tsedlmeier/Synthesizer/Ausarbeitung/src/content/5_VCO.tex

\chapter{VCO}
\label{ch:VCO}
\section{Allgemeines}

Der VCO stellt die Basis aller analogen Synthesizers da. 
Mit einem spannungsgesteuerten Oszillator lassen sich verschiedene Signale generieren, deren Frequenz sich mit der angelegten Steuerspannung verändert.
Analoge Synthesizer orientieren sich oft am 1V/Oktave-Standard.
Dieser besagt, dass sich die Frequenz des Signals mit jedem Volt verdoppelt.
Dies ist von Vorteil, da das Verhältnis zwischen Musiknoten und deren zugeordneten Frequenzen ebenfalls exponentiell ist.
Die tiefste C-Note entspricht beispielsweise einer Frequenz von 16,35 Hz.
Wenn man eine Oktave nach oben geht, verdoppelt sich die Frequenz beim nächsten C auf etwa 32 Hz. Typische Signale bei analogen Synthesizern können der Abbildung \ref{fig:Waveforms} entnommen werden. \cite{MakeSynth}

\begin{figure}[h]
	\centering
	\setlength{\fboxsep}{1pt} %Abstand der Linien zur Abbildung
	\setlength{\fboxrule}{1pt} %Dicke der Linie
	\fbox{}
	\caption{Typische Signale bei analogen Synthesizern \cite{MakeSynth}}
	\label{fig:Waveforms}
\end{figure}

Bei dieser Umsetzung des VCOs wurde sich auf die Realisierung eines Sägezahn- und eines Rechtecksignals konzentriert, da diese aufgrund ihrem hohen Oberwellenanteil markant-hörbare Geräusche erzeugen.
Ein Sinussignal hingegen stellt einen harmonischen Verlauf dar, der sich ebenfalls im Klang äußert.
Hörbare Schwingungen werden mithilfe einer Oszillatorschaltung realisiert, auf die im Folgenden näher eingegangen wird.

\begin{figure}[h]
	\centering
	\setlength{\fboxsep}{1pt} %Abstand der Linien zur Abbildung
	\setlength{\fboxrule}{1pt} %Dicke der Linie
	\fbox{}
	\caption{Oszillatorschaltung}
	\label{fig:Oszillatorschaltung}
\end{figure}

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

\begin{figure}[h]
	\centering
	\setlength{\fboxsep}{1pt} %Abstand der Linien zur Abbildung
	\setlength{\fboxrule}{1pt} %Dicke der Linie
	\fbox{}
	\caption{Oszillator Signalverlauf}
	\label{fig:Oszillator_Signalverlauf}
\end{figure}

\newpage

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

Die verwendete Schaltung in Abbildung \ref{fig:VCO_Stromlaufplan} ist zu großen Teilen an ein \textit{DIY VCO Kit} von Moritz Klein und Erica Synths angelehnt und wird im Folgenden näher erklärt. \cite{vco_manual}

\section{Schaltplan}
Wie im vorherigen Kapitel erläutert, erfolgt die Veränderung der Frequenz der Sägezahnschwingung (vgl. Abbildung  \ref{fig:Oszillator_Signalverlauf}) mithilfe eines NPN-Transistors, welcher im ersten Bereich des Schaltplans zu sehen ist. 
Der davor geschaltene PNP-Transistor dient zur Temperaturkompensation und fungiert als Emitterfolger, indem die an seiner Basis anliegende Spannung an den Emitter kopiert wird.
Allerdings ist die am Emitter des PNP-Transistors anliegende Spannung um der Schwellspannung des Transistors höher.
Bei Versuchen an der realen Schaltung betrug diese etwa 500 mV.
Um den gewünschten Spannungsbereich an der Basis des NPN-Transistors von etwa 350 -- 550 mV zu erreichen, muss das Potentiometer für die Einstellung der Basisspannung der Transistoren auch negative Spannungswerte liefern.

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

Um die resultierende Sägezahnschwingung nach außen führen zu können, wird ein entsprechender Buffer benötigt, der durch einen Operationsverstärker realisiert wird.
Dies ist zwingend notwendig, da ansonsten in die Funktionsweise der Oszillatorschaltung eingegriffen wird. 
Dieser Buffer befindet sich im dritten Bereich des Schaltplans.
Weiterhin wird eine AC-Kopplung mithilfe des Kondensators C2 und dem Widerstand R10 realisiert. 
Diese wird benötigt um eine eventuelle Offset-Spannung der Sägezahnspannung zu entfernen, damit das Signal um den definierten Pegel von 0 V schwingt.

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

Im fünften Bereich des Schaltplans erfolgt die Anpassung auf einen definierten Pegel von 10 V peak-to-peak. 
Da die Sägezahnschwingung eine geringe Spannung aufweist, wird diese mithilfe einer nicht invertierenden Verstärkerschaltung vergrößert und an den Klinkenbuchsenausgang \textit{SAW\_OUT} geführt. 
Da der Spannungspegel des Rechtecksignals durch die Komperatorschaltung verstärkt wurde, muss dieser mithilfe eines Spannungsteilers (R15, R18) entsprechend reduziert werden. 
Schließlich wird das Ausgangssignal durch einen Buffer an den Ausgang \textit{PULSE\_OUT} geführt.

Der nicht eingerahmte Bereich im Schaltplan umfasst die Spannungsversorgung. 
Mihilfe von Schottky-Dioden (D2, D3) wird der Verpolungsschutz der Eingangsspannung von $\pm$12 V gewährleistet. 
Durch die Stützkondensatoren (C3 -- C7) wird die Versorgungsspannung sowohl am Eingang der Spannungsversorgung am Wannenstecker als auch an den IC-Pins stabilisiert.
Weiterhin werden nicht verwendete Eingänge des Schmitt-Triggers mit Masse verbunden.

In der folgenden Tabelle werden die Ein- und Ausgabeelemente des VCOs zusammengefasst:

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

Nachdem die Funktionsweise der Schaltung auf einem Breadboard verifiziert wurde, wird ein Platinenlayout erstellt.
Auf die Vorgehensweise bei der Layouterstellung wird im folgenden Kapitel näher eingegangen.

\newpage
\begin{figure}[h]
\centering
\includepdf[angle=270, clip, trim=1cm 0.8cm 0.8cm 0.8cm, scale=0.8] {figures/VCO_Stromlaufplan_v2_unterteilt.pdf}
%\caption{In Bereiche unterteilter Schaltplan des Sequenzers}
\caption{Schaltplan VCO}
\label{fig:VCO_Stromlaufplan}
\end{figure}

\newpage

\section{Platine}
Nachdem der Schaltplan in Fusion 360 erstellt wurde und mit dem ERC (Electrical Rule Check)-Tool validiert wurde, erfolgt die Erstellung des Platinenlayouts (siehe Abbildung \ref{fig:VCO Layout}).
Die äußeren Abmaße der Platine sind in Bezug auf die Höhe eines \textit{Euro Racks} von 128,5 mm beschränkt. 
Gewählt wurde eine Platinenhöhe von 100 mm, damit ausreichend Platz zur Befestigung der Leiterplatte gewährleistet ist.

%\begin{figure}[h]
%	\centering
%	\setlength{\fboxsep}{1pt} %Abstand der Linien zur Abbildung
%	\setlength{\fboxrule}{1pt} %Dicke der Linie
%	\fbox{\includegraphics[width=0.5\textwidth]{figures/VCO_Layout}}
%	\caption{VCO Layout in Fusion 360}
%	\label{fig:VCO Layout}
%\end{figure}

\begin{figure}[h]
	\centering
	\begin{subfigure}{.5\textwidth}
		\centering
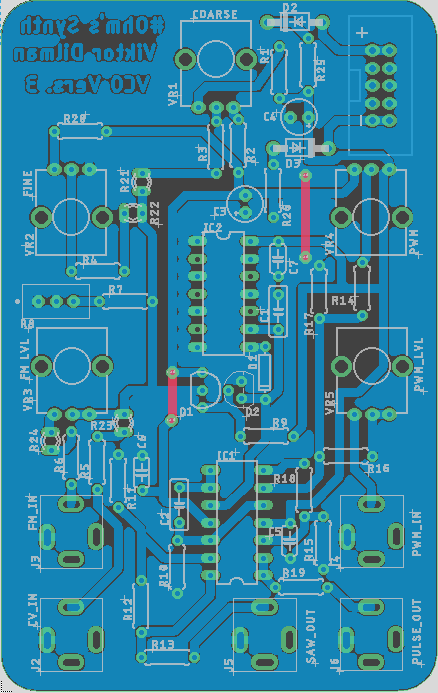
[picture p15: Ausarbeitung/src/figures/VCO_Layout_Front.png]
		
		\caption{Vorderseite}
		\label{fig:VCO_Leiterplatte_vorne}
	\end{subfigure}%
	\begin{subfigure}{.5\textwidth}
		\centering
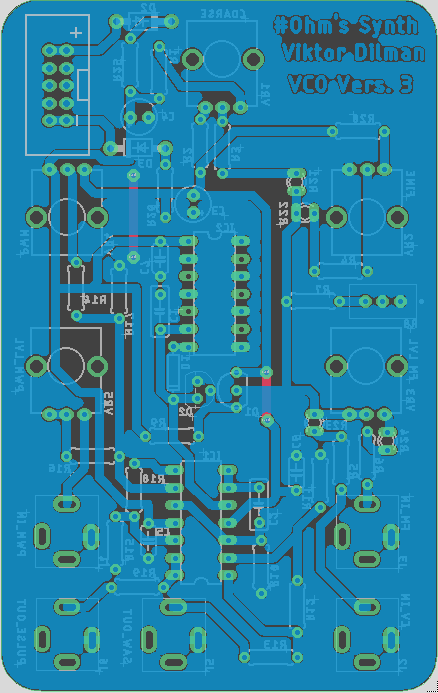
[picture p16: Ausarbeitung/src/figures/VCO_Layout_Back.png]
		
		\caption{Rückseite}
		\label{fig:VCO_Leiterplatte_hinten}
	\end{subfigure}
	\caption{VCO Layout in Fusion 360}
	\label{fig:VCO Layout}
\end{figure}

Die Bauteile wurden einerseits so positioniert, dass die Leiterbahnen möglichst kurz und überschneidungsfrei verlegt werden können.
Andererseits wurden die Potentiometer und Klinkenbuchsen logisch so angeordnet dass die zu einer Einbauklinkenbuchse gehörenden Potentiometer übereinander liegen.
Weiterhin wurde darauf geachtet, dass die Transistoren für die Temperaturkompensation möglichst nah aneinander positioniert werden.
Zudem sind die Stützkondensatoren der ICs möglichst nah an den Versorgungspins der Bauteile zu positionieren.

Bei der Erstellung der Platine wurde darauf geachtet möglichst eine Layer zu verwenden, um die Platine mit einer Platinenfräse herstellen zu können.
Dies ist von Vorteil, da bei der professionellen Anfertigung von Platinen von der Bestellung bis zur Lieferung einige Wochen vergehen können.
Ist der Zugang zu einer Fräse gegeben, kann die erstellte Platine sofort getestet und eventuelle Fehler ausgebessert werden.

Damit die Leiterplatte mit einer Platinenfräse angefertigt werden kann, ist eine relativ dicke Leiterbahnbreite erforderlich. 
Gewählt wurde deshalb eine Leiterbrahnbreite von 50 mil.
An den Stellen, an denen die Leiterbahnen nicht überschneidungsfrei verlegt werden konnten, wurden \textit{Vias} hinzugefügt und die Leiterbahn auf der anderen Seite fortgeführt.
Auf der gefrästen Platinen (siehe Abbildung \ref{fig:VCO Leiterplatte gefraest}) können diese \textit{Vias} mit Brücken verbunden werden.

\begin{figure}[h]
	\centering
	\setlength{\fboxsep}{1pt} %Abstand der Linien zur Abbildung
	\setlength{\fboxrule}{1pt} %Dicke der Linie
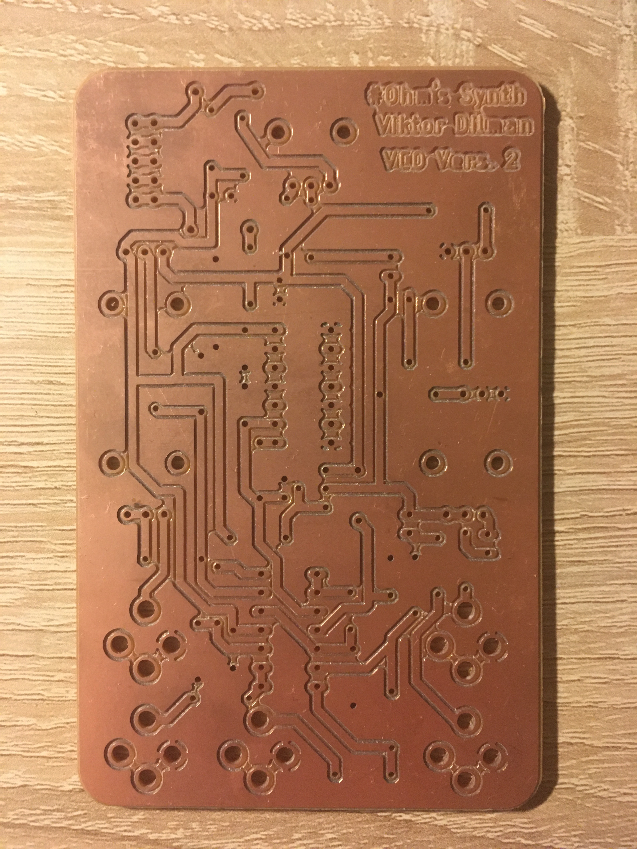
[picture p17: Ausarbeitung/src/figures/VCO_Leiterplatte_gefraest.JPG]
	\fbox{}
	\caption{Gefräste VCO Leiterplatte}
	\label{fig:VCO Leiterplatte gefraest}
\end{figure}

Da für die verwendeten Einbauklinkenbuchsen keine passende Bibliothek existiert, musste diese manuell angelegt werden.
Dafür wurde ein Symbol einer ähnlichen Klinkenbuchse verwendet und das Footprint nach dem Datenblatt des Herstellers erstellt wie in Abbildung \ref{fig:Einbauklinkenbuchse in Fusion 360} zu sehen. \cite{cliff}

\begin{figure}[h]

\end{figure}

\begin{figure}[h]
	\centering
	\begin{subfigure}{.5\textwidth}
	\centering
	\setlength{\fboxsep}{1pt} %Abstand der Linien zur Abbildung
	\setlength{\fboxrule}{1pt} %Dicke der Linie
	\fbox{}
	\caption{Verwendetes Symbol}
	\label{fig:Klinkenbuchse Symbol}
	\end{subfigure}%
	\begin{subfigure}{.5\textwidth}
	\centering
	\setlength{\fboxsep}{1pt} %Abstand der Linien zur Abbildung
	\setlength{\fboxrule}{1pt} %Dicke der Linie
	\fbox{}
	\caption{Erstelltes Footprint}
	\label{fig:Klinkenbuchse Footprint}
	\end{subfigure}
	\caption{Erstellung der Einbauklinkenbuchse in Fusion 360}
	\label{fig:Einbauklinkenbuchse in Fusion 360}
\end{figure}

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

\begin{figure}[h]
	\centering
	\begin{subfigure}{.5\textwidth}
		\centering
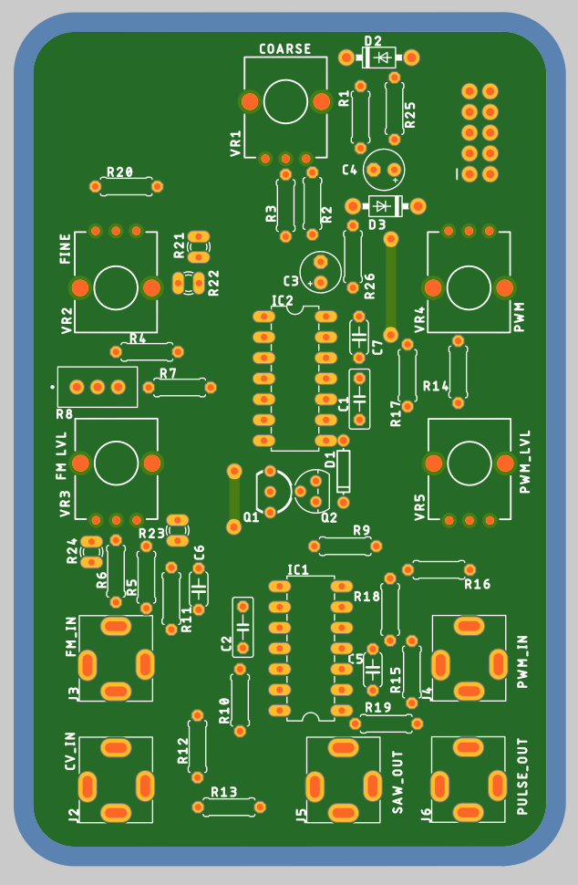
[picture p18: Ausarbeitung/src/figures/VCO_Rendering_Front.png]
		
		\caption{Vorderseite}
		\label{fig:VCO_Front}
	\end{subfigure}%
	\begin{subfigure}{.5\textwidth}
		\centering
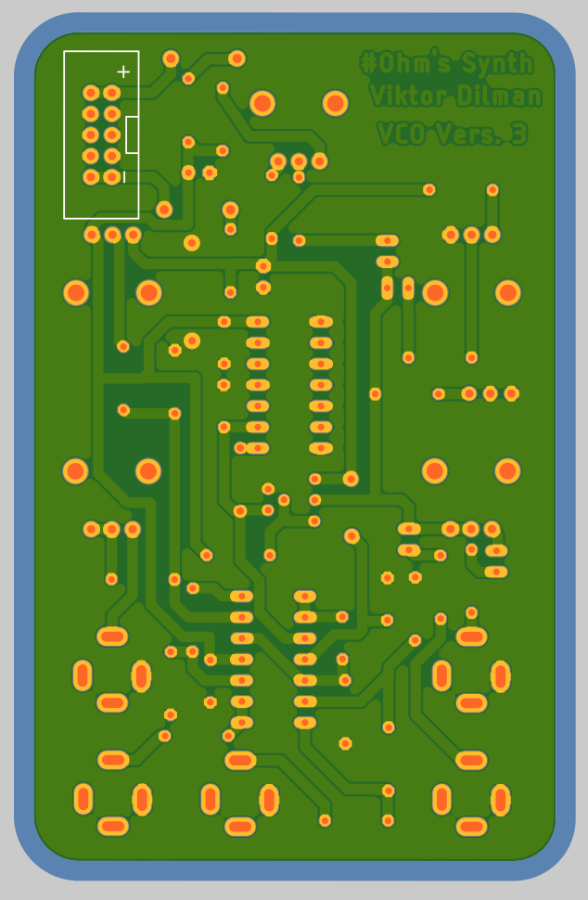
[picture p19: Ausarbeitung/src/figures/VCO_Rendering_Back.png]
		
		\caption{Rückseite}
		\label{fig:VCO_Back}
	\end{subfigure}
	\caption{VCO Leiterplatte}
	\label{fig:VCO Leiterplatte}
\end{figure}

\newpage
\section{Mechanischer Aufbau}
Mithilfe der \textit{Fusion 360}-Funktionalität der Übertragung einer 2D- auf eine 3D-Leiterplatte wurde eine Abdeckung konstruiert (siehe Abbildung \ref{fig:VCO Frontplattemit 3D-Leiterplatte}).
Dies hat den Vorteil, dass für die Potentiometer und Klinkenbuchsen die Aussparungen an der Frontplatte exakt positioniert werden können.
Die Abdeckplatte wird mithilfe von Gewindeschrauben der Einbauklinkenbuchsen an die Platine befestigt.
Weiterhin werden auf die Potentiometer Abdeckkappen angebracht, die zusätzlichen Halt bieten.
An den Ecken der Frontplatte werden Aussparungen vorhergesehen, um das Modul in einem Eurorack-Gehäuse befestigen zu können.
Schließlich wird die Frontplatte aus Plexiglas mit einem \textit{Laser-Cutter} gefertigt.

\begin{figure}[h]
	\centering
	\setlength{\fboxsep}{1pt} %Abstand der Linien zur Abbildung
	\setlength{\fboxrule}{1pt} %Dicke der Linie
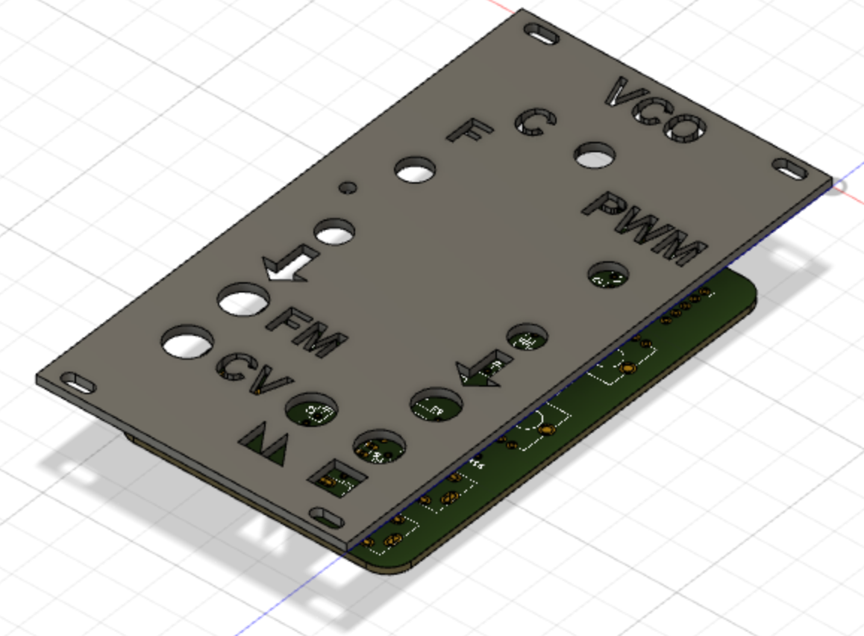
[picture p20: Ausarbeitung/src/figures/VCO_Frontplatte_schraeg.png]
	\fbox{}
	\caption{VCO Frontplatte schräg mit Leiterplatte}
	\label{fig:VCO Frontplattemit 3D-Leiterplatte}
\end{figure}

%\begin{figure}[h]
%	\centering
%	\setlength{\fboxsep}{1pt} %Abstand der Linien zur Abbildung
%	\setlength{\fboxrule}{1pt} %Dicke der Linie
%	\fbox{\includegraphics[width=0.35\textwidth]{figures/VCO_Frontplatte_oben}}
%	\caption{VCO Frontplatte, Vorderansicht}
%	\label{fig:VCO Frontplatte}
%\end{figure}
