tsedlmeier/Synthesizer/Sonstiges/LPDES/VCO_Studienarbeit_Latex/Änderung in thesis.tex und cover.txt

Die Welt der Technik befindet sich seit Beginn in einem ständigen Wandel. Neben immer komplexer und kleinerer werdender Hardware steigen auch stetig die Anforderung bezüglich leistungsfähiger und flexibler Software. Besonders die Verarbeitungsgeschwindigkeit und Reaktionsfähigkeit von Software-Systemen rückt dabei zunehmend in den Fokus. So haben in den Anfangszeiten der Informatik gerade sequentiel oder seriel abarbeitende Programme Anwendung gefunden. Dies bedeutet, dass jeder Befehl Zeile für Zeile abgearbeitet wurde. Die Abarbeitung entspricht einem linearen Vorgehen. Für viele Anwendungen ist dieses Verhalten jedoch gänzlich ungeeignet. Somit etablierte sich neben der sequentiellen Abarbeitung zunehmend die parallele oder quasiparallele Abarbeitung. Gerade bei den heutigen Mikrocontroller- oder Prozessor-Familien werden mit geschickten Scheduling-Mechanismen die vielfälltig einsetzbaren eingebetten Systeme, die beinahe in jeden Bereich des Altags vorgedrungen sind, erst möglich. In Python sind diese Werkzeuge in Form von Koroutinen, Threads oder Asnychio auf Programmierebene gegeben. Sinnvoll und bedacht eingesetzt können sie merkliche Geschwindigkeits- und Flexibilitätsvorteile für den Anwender erbringen.\\
Neben der grundlegenden theoretischen Erläuterung der verscheidenen Konzepte sollen durch die nähere Betrachtung eines exemplarischen Anwendungsfalls die Zusammenhänge besser verdeutlicht werden.
