tsedlmeier/Synthesizer/Sonstiges/LPDES/VCO_Studienarbeit_Latex/thesis-template-master/thesis.tex

\documentclass[
    11pt,
    a4paper,
    egregdoesnotlikesansseriftitles,
    toc=chapterentrywithdots,
    openany,
    oneside,
    titlepage,
    parskip=half,
    headings=normal,  % reduces heading size
    listof=totoc,
    bibliography=totoc,
    index=totoc,
    captions=tableheading,  % caption below table
    chapterprefix,
    listof=flat,
    final
]{scrbook}

% details about your thesis
\newcommand{\titel}{
	Entwicklung eines modularen Synthesizers: Voltage Controlled Oscillator}
\newcommand{\artderarbeit}{Studienarbeit}  % {Projektarbeit, Bachelorarbeit,Masterarbeit}
\newcommand{\autor}{
	%Altaher Ahmad, Balbach Thomas, 
	Dilman Viktor
	%, Kirschner Christoph, Sedlmeier Toni 
}
\newcommand{\studiengang}{Fach Leiterplattendesign}  % {Informatik,Wirtschaftsinformatik,Medieninformatik}
%\newcommand{\ausgabe}{22.12.2022}
\newcommand{\abgabe}{ 22.12.2022}
\newcommand{\erstgutachter}{
	%Prof. Dr.Alexander von Hoffmann 
	M.Eng. Eduard Bluoss
}
\newcommand{\logo}{figures/TH-Nuernberg-RGB.png}
\newcommand{\keywords}{hot, fuzz}

% custom head and foot
\usepackage[automark]{scrlayer-scrpage}
\pagestyle{scrheadings}
\ihead{\headmark}
\chead{}
\ohead{\pagemark}
\renewcommand*\chaptermarkformat{\chapappifchapterprefix{\ }% 
  \thechapter.\enskip}

\usepackage{titlesec}

\RedeclareSectionCommand[tocindent=0pt]{section}
\RedeclareSectionCommand[tocindent=0pt]{subsection}
\RedeclareSectionCommand[tocnumwidth=30pt, beforeskip = -30pt]{chapter}

\usepackage{scrhack}

% other packages
\usepackage[utf8]{inputenc}
\usepackage[T1]{fontenc}
\usepackage{lmodern,relsize,textcomp,csquotes}
\usepackage{amsmath,amsfonts}
\usepackage[ngerman,ngerman]{babel}  % flip for German thesis
\usepackage[final]{graphicx}
\usepackage{setspace,geometry,xcolor}
\usepackage{makeidx}
\usepackage{paralist,ifthen,todonotes}
\usepackage{url}
%\usepackage[toc]{glossaries}
\usepackage{pdfpages}
\usepackage[style = numeric, backend = bibtex]{biblatex}
%Für die Nutzung von Abkürzungen
\usepackage{acronym}
%Für die Nutzung von setlist im Abkürzungsverzeichnis
\usepackage{enumitem}

%\usepackage[demo]{graphicx}
\usepackage{caption}
\usepackage{subcaption}

% table setup
\usepackage{longtable}
\usepackage{array}
\usepackage{ragged2e}
\usepackage{lscape}

% pdf hyperref
\usepackage[
    bookmarks=true,
    bookmarksopen=true,
    bookmarksnumbered=true,
    bookmarksopenlevel=1,
    pdftitle={\titel},
    pdfauthor={\autor},
    pdfcreator={\autor},
    pdfsubject={\titel},
    pdfkeywords={\keywords},
    pdfpagelabels=true,
    colorlinks=true,
    linkcolor=red,
    urlcolor=magenta,
    citecolor=cyan,
    filecolor=magenta,
    menucolor=red,
    plainpages=false,
    hypertexnames=true,
    linktocpage=true,
]{hyperref}

% configure your listings style
\usepackage{listings}
\lstset{
	tabsize=3,
	extendedchars=true,
	frame=single,
	showstringspaces=true,
	numbers=left,
	numberstyle=\small,
	breakautoindent=true,
	basicstyle=\small
}

\renewcommand{\lstlistingname}{Auflistung} % Aendert Listing zu Auflistung
\renewcommand{\lstlistlistingname}{Auflistungsverzeichnis} % Aendert Listing zu Auflistung

% page setup
% \setlength{\topskip}{\ht\strutbox}
\geometry{paper=a4paper,left=3cm,top=2cm,right=2cm,bottom=2cm}
\onehalfspacing
\frenchspacing
\clubpenalty = 10000
\widowpenalty = 10000 
\displaywidowpenalty = 10000

% some commands
\newcommand{\ua}{\mbox{u.\,a.\ }}
\newcommand{\zB}{\mbox{z.\,B.\ }}
\newcommand{\dahe}{\mbox{d.\,h.,\ }}
\newcommand{\bzw}{\mbox{bzw.\ }}
\newcommand{\bzgl}{\mbox{bzgl.\ }}
\newcommand{\eg}{\mbox{e.\,g.\ }}
\newcommand{\ie}{\mbox{i.\,e.\ }}
\newcommand{\wrt}{\mbox{w.\,r.\,t.\ }}
\newcommand{\etal}{\mbox{\emph{et.\,al.\ }}}

% load glossary entries
%\makenoidxglossaries
%\loadglsentries{glossary}

%\bibliographystyle{ieeetran}
\bibliography{refs.bib}
\nocite{*}

\begin{document}

\setcounter{secnumdepth}{3}  % numerate subsections
\setcounter{tocdepth}{2}  % ...but don't include them in toc

\frontmatter
\include{cover}\cleardoublepage

%\include{content/0_abstract}\cleardoublepage

%\titleformat{\chapter}
%  {\Large\bfseries} % format
%  {}                % label
%  {0pt}             % sep
%  {\huge}           % before-code
%  
%\tableofcontents\cleardoublepage

\tableofcontents

\include{Abkuerzungsverzeichnis/abkuerzungsverzeichnis}

\listoffigures

\listoftables

\mainmatter
\include{content/1_intro}
\include{content/2_concepts}
%\include{content/3_Netzteil}
%\include{content/4_LFO}
\include{content/5_VCO}
%\include{content/6_Sequenzer}
%\include{content/7_Filter}
%\include{content/8_Mischer}
%\include{content/9_Gehauese}
%\include{content/10_summary}

% remove if not needed
%\appendix
%\include{content/a1_supplemental}

%\backmatter

%\lstlistoflistings
%\cleardoublepage

%\printbibliography
\printbibliography[heading=bibintoc, title={Literaturverzeichnis}]
\end{document}
