tsedlmeier/Synthesizer/Ausarbeitung/src/content/8_Mischer.tex

\chapter{Mischer}
\label{ch:concept}
\section{Allgemeines}
Der Audio Mixer verknüpft verschiedene, von den anderen Bauteilen des modularen Synthesizers erzeugte Eingangssignale (Klangquellen) miteinander. Das heißt er mischt, kombiniert und gleicht verschiedene Klänge und Audiosignale aus, wodurch neue Signalformen
und Klänge generiert werden können. Die entstehenden kombinierten Signale werden an den Filter weitergeleitet.

\section{Schaltplan}
Dieser Abschnitt beschreibt den Schaltplan des Mischers in Abbildung \ref{fig:schaltplan_mixer}. 
Dazu werden die einzelnen Teilbereiche des Schaltplans vorgestellt.

IN1-IN3 sind die Audioeingangsbuchsen, INV OUT-CLIP OUT sind die Audio-Ausgangsbuchsen.

Der Teilbereich 1 des Schaltplans ermöglicht die Anpassung der Lautstärke der Signale in jedem Bereich zwischen 0\% und 100\%. 
Ein zentrales Bauteil ist der Vierfach-Operationsverstärker TL074P. Die drei verbauten Potentiometer regeln die Levels der Eingangssignale.

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

\begin{figure}[h]
	\centering
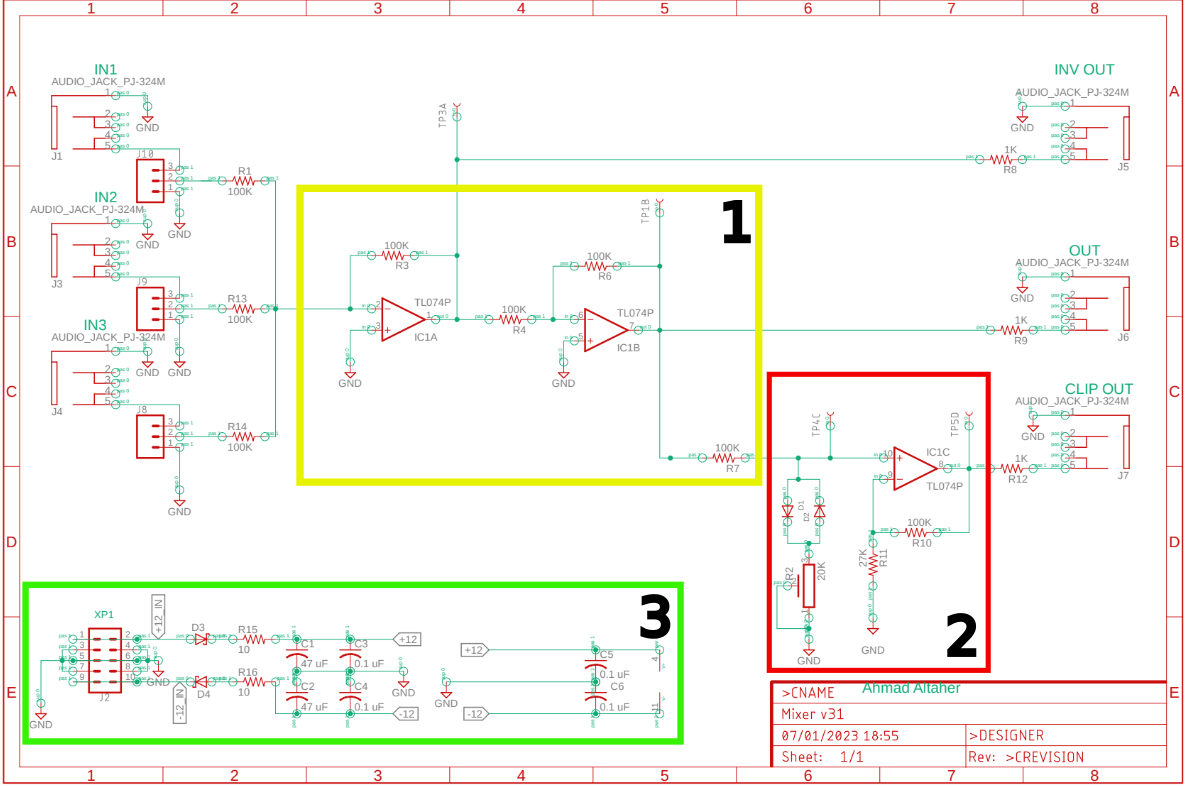
[picture p78: Ausarbeitung/src/figures/SchaltplanMixer_new.png]
	
	\caption{Ausschnitt des Mischer-Schaltplanes aus Fusion360 \cite{mixer_manual}}
	\label{fig:schaltplan_mixer}
\end{figure}
\FloatBarrier

\section{Platine}
\begin{figure}[h]
	\centering
	\setlength{\fboxsep}{1pt} %Abstand der Linien zur Abbildung
	\setlength{\fboxrule}{1pt} %Dicke der Linie
	\fbox{}
	\caption{Ausschnitt des Mischer-Platinen-Layouts aus Fusion360 (Unterseite)}
	\label{fig:platine_mixer}
\end{figure}
\FloatBarrier
