tsedlmeier/Synthesizer/Bauteile/Bauteilliste_Synth_181022.docx

Bauteilliste (zusätzlich zur Moritz-Klein-Bauteilliste), validiert

Bauteil | Stück | | Website | | Artikel-Nr. | Link

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

LFO
Widerstände 220kohm | 20 | | Reichelt | | METALL 220K | https://www.reichelt.de/de/de/widerstand-metallschicht-220-kohm-0207-0-6-w-1--metall-220k-p11628.html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
Widerstände 100kohm | 10 | | Reichelt | | METALL 100K | https://www.reichelt.de/widerstand-metallschicht-100-kohm-0207-0-6-w-1--metall-100k-p11458.html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
Widerstände 51kohm | 20 | | Reichelt | | METALL 51,0K | https://www.reichelt.de/widerstand-metallschicht-51-0-kohm-0207-0-6-w-1--metall-51-0k-p11859.html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
Widerstände 22kohm | 20 | | Reichelt | | METALL 22,0K | https://www.reichelt.de/widerstand-metallschicht-22-0-kohm-0207-0-6-w-1--metall-22-0k-p11622.html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
Widerstände 20kohm | 20 | | Reichelt | | METALL 20,0K | https://www.reichelt.de/widerstand-metallschicht-20-0-kohm-0207-0-6-w-1--metall-20-0k-p11606.html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
Widerstände 10kohm | 20 | | Reichelt | | METALL 10,0K | https://www.reichelt.de/widerstand-metallschicht-10-0-kohm-0207-0-6-w-1--metall-10-0k-p11449.html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
Widerstände 1kohm | 20 | | Reichelt | | METALL 1,00K | https://www.reichelt.de/widerstand-metallschicht-1-00-kohm-0207-0-6-w-1--metall-1-00k-p11403.html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
Widerstände 100Ohm | 20 | | Reichelt | | METALL 100 | https://www.reichelt.de/widerstand-metallschicht-100-ohm-0207-0-6-w-1--metall-100-p11457.html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
Kondensatoren 1uF | 10 | | Reichelt | | Z5U-5 1,0µ | https://www.reichelt.de/vielschicht-keramikkondensator-1-0-20--z5u-5-1-0--p22985.html
Dioden SB140 (Schottky) | 5 | | Reichelt | | SB 140 | https://www.reichelt.de/schottkydiode-40-v-1-a-do-41-sb-140-p16024.html
Transistoren BC548 (NPN) | 5 | | Reichelt | | BC 548C | https://www.reichelt.de/de/de/bipolartransistor-npn-30v-0-1a-0-5w-to-92-bc-548c-p5010.html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
Transistoren BC558 (PNP) | 5 | | Reichelt | | BC 558A | https://www.reichelt.de/de/de/bipolartransistor-pnp-30v-0-1a-0-5w-to-92-bc-558a-p5020.html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
Potentiometer 100k vertikal | 3 | | Reichelt | | RK09K113-LIN100K | https://www.reichelt.de/drehpotentiometer-mono-100-kohm-linear-6-mm-rk09k113-lin100k-p73818.html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
LED GRÜN | 10 | | Reichelt | | LED 5MM ST GN | https://www.reichelt.de/led-5-mm-bedrahtet-gruen-20-mcd-60--led-5mm-st-gn-p6823.html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
LED ROT | 10 | | Reichelt | | LED 5MM ST RT | https://www.reichelt.de/led-5-mm-bedrahtet-rot-5-mcd-60--led-5mm-st-rt-p6821.html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
ICs TL074 | 5 | | Reichelt | | TL 074 DIL | https://www.reichelt.de/operationsverstaerker-4-fach-dip-14-tl-074-dil-p21557.html
EBS 35 Klinkeneinbaubuchse | 5 | | Reichelt | | EBS 35 | https://www.reichelt.de/klinkeneinbaubuchse-3-5-mm-stereo-ebs-35-p7301.html?&trstct=pos_0&nbc=1
Kippschalter, Ein-Ein | 5 | | Reichelt | | GOOBAY 10020 | https://www.reichelt.de/kippschalter-c7584.html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

Sequencer
Widerstände 100kohm | 20 | | Reichelt | | METALL 100K | https://www.reichelt.de/widerstand-metallschicht-100-kohm-0207-0-6-w-1--metall-100k-p11458.html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
Widerstände 68 kohm | 10 | | Reichelt | | YAG 4FTE52-68K | https://www.reichelt.de/widerstand-metallschicht-68-kohm-0204-0-4-w-1--yag-4fte52-68k-p236962.html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
Widerstände 51kohm | 10 | | Reichelt | | METALL 51,0K | https://www.reichelt.de/widerstand-metallschicht-51-0-kohm-0207-0-6-w-1--metall-51-0k-p11859.html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
Widerstände 47 kohm | 10 | | Reichelt | | METALL 47,0K | https://www.reichelt.de/widerstand-metallschicht-47-0-kohm-0207-0-6-w-1--metall-47-0k-p11823.html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
Widerstände 18 kohm | 10 | | Reichelt | | METALL 18,0K | https://www.reichelt.de/widerstand-metallschicht-18-0-kohm-0207-0-6-w-1--metall-18-0k-p11558.html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
Widerstände 6,8 kohm | 10 | | Reichelt | | YAG FTE52-6K80 | https://www.reichelt.de/widerstand-metallschicht-6-8-kohm-0204-0-4-w-1--yag-fte52-6k80-p236939.html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
Widerstände 4,7 kohm | 10 | | Reichelt | | METALL 4,70K | https://www.reichelt.de/widerstand-metallschicht-4-70-kohm-0207-0-6-w-1--metall-4-70k-p11784.html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
Widerstände 1 kohm | 10 | | Reichelt | | METALL 1,00K | https://www.reichelt.de/widerstand-metallschicht-1-00-kohm-0207-0-6-w-1--metall-1-00k-p11403.html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
Widerstände 200 ohm | 10 | | Reichelt | | METALL 200 | https://www.reichelt.de/widerstand-metallschicht-200-ohm-0207-0-6-w-1--metall-200-p11609.html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
Widerstände 10 ohm | 10 | | Reichelt | | METALL 10,0 | https://www.reichelt.de/widerstand-metallschicht-10-0-ohm-0207-0-6-w-1--metall-10-0-p11448.html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
Elektrolytkondensatoren 47uF | 10 | | Reichelt | | RAD LXZ 16/47 | https://www.reichelt.de/elko-radial-47-f-16-v-105-low-esr-5x11-5-mm-rm-2-5-rad-lxz-16-47-p166362.html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
Folienkondensator, 1 µF | 10 | | Reichelt | | ECWFE 1U 450 | https://www.reichelt.de/folienkondensator-1-f-450-v-rm-15-105-c-5--ecwfe-1u-450-p228877.html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
Keramik-Kondensator, 100 nF | 10 | | Reichelt | | KERKO 100N | https://www.reichelt.de/keramik-kondensator-100-nf-20-80-y5v-50-100-v-rm-5-kerko-100n-p9265.html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
Keramik-Kondensator 1,0N | 10 | | Reichelt | | KERKO 1,0N | https://www.reichelt.de/keramik-kondensator-1-0n-kerko-1-0n-p9257.html?&trstct=pol_0&nbc=1
Schottkydiode | 10 | | Reichelt | | SB 140 | https://www.reichelt.de/schottkydiode-40-v-1-a-do-41-sb-140-p16024.html
Dioden 1N4148 | 30 | | Reichelt | | 1N 4148 | https://www.reichelt.de/schalt-diode-100-v-150-ma-do-35-1n-4148-p1730.html?&trstct=pos_0&nbc=1
Bipolartransistor, NPN | 10 | | Reichelt | | 2N 3904 | https://www.reichelt.de/bipolartransistor-npn-40v-0-2a-0-5w-to-92-2n-3904-p2020.html
Bipolartransistor, NPN | 10 | | Reichelt | | BC 547B | https://www.reichelt.de/bipolartransistor-npn-45v-0-1a-0-5w-to-92-bc-547b-p5006.html?&trstct=pos_1&nbc=1
Drehpotentiometer, 250 kOhm, linear, 6 mm | 2 | | Reichelt | | PIH PC16IP06254A | https://www.reichelt.de/drehpotentiometer-250-kohm-linear-6-mm-pih-pc16ip06254a-p232706.html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
Drehpotentiometer, Mono, 100 kOhm, linear, 6 mm | 5 | | Reichelt | | RK09K111-LIN100K | https://www.reichelt.de/drehpotentiometer-mono-100-kohm-linear-6-mm-rk09k111-lin100k-p73810.html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
Kippschalter, Ein-Ein | 10 | | Reichelt | | GOOBAY 10020 | https://www.reichelt.de/kippschalter-c7584.html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
LED 5 mm - Farbe Blau, 100 Stück | 1 | | Reichelt | | QUAD 1802O025 | https://www.reichelt.de/led-5-mm-farbe-blau-100-stueck-quad-1802o025-p280131.html?&trstct=pos_2&nbc=1
ICs TL074 | 5 | | Reichelt | | TL 074 DIL | https://www.reichelt.de/operationsverstaerker-4-fach-dip-14-tl-074-dil-p21557.html
SMD 4017 Counter | 5 | | Reichelt | | 4017BE TEX | https://www.reichelt.de/counter-5-stage-3--18-v-dil-16-cd-4017be-tex-p216643.html?search=cd4017
Potentiometer 5k | 5 | | Reichelt | | 76-10 5,0K | https://www.reichelt.de/praezisionspotentiometer-trimmer-liegend-5-0-kohm-9-5-mm-76-10-5-0k-p3496.html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
Potentiometer 2k | 5 | | Reichelt | | 76-10 2,0K | https://www.reichelt.de/praezisionspotentiometer-trimmer-liegend-2-0-kohm-9-5-mm-76-10-2-0k-p3494.html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
MONTAGERING 5MM | 50 | | Reichelt | | MONTAGERING 5MM | https://www.reichelt.de/montageclip-fuer-5-mm-leds-montagering-5mm-p12529.html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
EBS 35 Klinkeneinbaubuchse | 5 | | Reichelt | | EBS 35 | https://www.reichelt.de/klinkeneinbaubuchse-3-5-mm-stereo-ebs-35-p7301.html?&trstct=pos_0&nbc=1

VCA
Widerstände 100kohm | 20 | | Reichelt | | METALL 100K | https://www.reichelt.de/widerstand-metallschicht-100-kohm-0207-0-6-w-1--metall-100k-p11458.html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
Widerstände 82 kohm | 20 | | Reichelt | | METALL 82,0K | https://www.reichelt.de/widerstand-metallschicht-82-0-kohm-0207-0-6-w-1--metall-82-0k-p11999.html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
Widerstände 20 kohm | 20 | | Reichelt | | METALL 20,0K | https://www.reichelt.de/widerstand-metallschicht-20-0-kohm-0207-0-6-w-1--metall-20-0k-p11606.html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
Widerstände 10kohm | 20 | | Reichelt | | METALL 10,0K | https://www.reichelt.de/widerstand-metallschicht-10-0-kohm-0207-0-6-w-1--metall-10-0k-p11449.html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
Widerstände 1 kohm | 20 | | Reichelt | | METALL 1,00K | https://www.reichelt.de/widerstand-metallschicht-1-00-kohm-0207-0-6-w-1--metall-1-00k-p11403.html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
Widerstände 10 ohm | 20 | | Reichelt | | METALL 10,0 | https://www.reichelt.de/widerstand-metallschicht-10-0-ohm-0207-0-6-w-1--metall-10-0-p11448.html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
Widerstände 100 ohm | 20 | | Reichelt | | METALL 100 | https://www.reichelt.de/widerstand-metallschicht-100-ohm-0207-0-6-w-1--metall-100-p11457.html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
Kondensatoren; 47uF | 7 | | Reichelt | | M 47U 25 | https://www.reichelt.de/elko-radial-47-f-25-v-rm-2-85-c-2000-h-20--m-47u-25-p228351.html?&trstct=pos_1&nbc=1
Kondensator, 100nF | 20 | | Reichelt | | X7R-5 100N | https://www.reichelt.de/vielschicht-kerko-100-nf-50-100-v-x7r-10-rm-5-0-x7r-5-100n-p22865.html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
Dioden SB140 (Schottky | 5 | | Reichelt | | SB 140 | https://www.reichelt.de/schottkydiode-40-v-1-a-do-41-sb-140-p16024.html
Transistoren BC548 (NPN) | 7 | | Reichelt | | BC 548C | https://www.reichelt.de/de/de/bipolartransistor-npn-30v-0-1a-0-5w-to-92-bc-548c-p5010.html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
Potentiometer 100k | 3 | | Reichelt | | RK09K113-LIN100K | https://www.reichelt.de/drehpotentiometer-mono-100-kohm-linear-6-mm-rk09k113-lin100k-p73818.html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
ICs TL074 | 5 | | Reichelt | | TL 074 DIL | https://www.reichelt.de/operationsverstaerker-4-fach-dip-14-tl-074-dil-p21557.html

Netzteil
µA 7812 Spannungsregle | 5 | | Reichelt | | µA 7812 | https://www.reichelt.de/spannungsregler-fest-11-5--12-5-v-to-220--a-7812-p23455.html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
µA 7912 Spannungsregler | 5 | | Reichelt | | µA 7912 | https://www.reichelt.de/spannungsregler-fest-11-5--12-5-v-to-220--a-7912-p31189.html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
1N4007 rectifier diode | 20 | | Reichelt | | 1N 4007-T DII | https://www.reichelt.de/gleichrichterdiode-1000-v-1-a-do-41-1n-4007-t-dii-p219376.html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
Radialer Elektrolytkondensator 4.700µF | 10 | | Reichelt | | RAD 4.700/35 | https://www.reichelt.de/elko-radial-4700-f-35-v-rm-7-5-85-c-2000h-20--rad-4-700-35-p15140.html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
1 uF Kondensator | 6 | | Reichelt | | T356 1,0U 35 | https://www.reichelt.de/tantal-bedrahtet-1-0-f-35v-85-c-t356-1-0u-35-p206422.html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
CHANCS Netzteil Eingang AC 220V Ausgang AC 12V Netzteil Adapter für Haushaltsgeräte | 1 | | Amazon | | | https://www.amazon.de/CHANCS-Netzteil-Eingang-Ausgang-Haushaltsger%C3%A4te/dp/B08HQB2J9B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
WSL 10G Wannenstecker, 10-polig | 20 | | Reichelt | | WSL 10G | https://www.reichelt.de/wannenstecker-10-polig-gerade-wsl-10g-p22816.html?&trstct=pos_0&nbc=1
Pfostenbuchse, 10-polig | 20 | | Reichelt | | PFL 10 | https://www.reichelt.de/pfostenbuchse-10-polig-mit-zugentlastung-pfl-10-p14571.html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

Mischer
Widerstände 100kohm | 20 | | Reichelt | | METALL 100K | https://www.reichelt.de/widerstand-metallschicht-100-kohm-0207-0-6-w-1--metall-100k-p11458.html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
Widerstände 1 kohm | 20 | | Reichelt | | METALL 1,00K | https://www.reichelt.de/widerstand-metallschicht-1-00-kohm-0207-0-6-w-1--metall-1-00k-p11403.html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
Widerstände 10 ohm | 20 | | Reichelt | | 2W METALL 10 | https://www.reichelt.de/widerstand-metalloxidschicht-10-ohm-0414-2-w-5--2w-metall-10-p2311.html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
Widerstände 1 kohm | 20 | | Reichelt | | METALL 1,00K | https://www.reichelt.de/widerstand-metallschicht-1-00-kohm-0207-0-6-w-1--metall-1-00k-p11403.html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
Kondensatoren; 47uF | 7 | | Reichelt | | M 47U 25 | https://www.reichelt.de/elko-radial-47-f-25-v-rm-2-85-c-2000-h-20--m-47u-25-p228351.html?&trstct=pos_1&nbc=1
Folienkondensator, 100nF | 20 | | Reichelt | | MKS4-50 100N | https://www.reichelt.de/folienkondensator-100nf-50v-rm7-5-mks4-50-100n-p172750.html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
Dioden SB140 (Schottky | 5 | | Reichelt | | SB 140 | https://www.reichelt.de/schottkydiode-40-v-1-a-do-41-sb-140-p16024.html
Dioden 1N4148 | 30 | | Reichelt | | 1N 4148 | https://www.reichelt.de/schalt-diode-100-v-150-ma-do-35-1n-4148-p1730.html?&trstct=pos_0&nbc=1
Potentiometer 100k | 5 | | Reichelt | | RK09K113-LIN100K | https://www.reichelt.de/drehpotentiometer-mono-100-kohm-linear-6-mm-rk09k113-lin100k-p73818.html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
20K Präzisionspotentiometer | 5 | | Reichelt | | 76-10 20K | https://www.reichelt.de/praezisionspotentiometer-trimmer-liegend-20-kohm-9-5-mm-76-10-20k-p3495.html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
EBS 35 Klinkeneinbaubuchse | 5 | | Reichelt | | EBS 35 | https://www.reichelt.de/klinkeneinbaubuchse-3-5-mm-stereo-ebs-35-p7301.html?&trstct=pos_0&nbc=1
ICs TL074 | 5 | | Reichelt | | TL 074 DIL | https://www.reichelt.de/operationsverstaerker-4-fach-dip-14-tl-074-dil-p21557.html

# Noise/S&H

Widerstände 1Mohm | 10 | | Reichelt | | ARC MRA0207 1M B | https://www.reichelt.de/widerstand-metallschicht-1-0-mohm-0207-250-mw-0-1--arc-mra0207-1m-b-p237509.html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
Widerstände 470 Kohm | 20 | | | | METALL 470K | https://www.reichelt.de/widerstand-metallschicht-470-kohm-0207-0-6-w-1--metall-470k-p11827.html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
Widerstände 100kohm | 20 | | Reichelt | | METALL 100K | https://www.reichelt.de/widerstand-metallschicht-100-kohm-0207-0-6-w-1--metall-100k-p11458.html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
Widerstände 51kohm | 20 | | Reichelt | | METALL 51,0K | https://www.reichelt.de/widerstand-metallschicht-51-0-kohm-0207-0-6-w-1--metall-51-0k-p11859.html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
Widerstände 47 kohm | 20 | | Reichelt | | 1W 47K | https://www.reichelt.de/widerstand-metalloxyd-47-kohm-0207-1-0-w-5--1w-47k-p1827.html
Widerstände 33 kohm | 20 | | Reichelt | | METALL 33,0K | https://www.reichelt.de/widerstand-metallschicht-33-0-kohm-0207-0-6-w-1--metall-33-0k-p11730.html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
Widerstände 22kohm | 20 | | Reichelt | | METALL 22,0K | https://www.reichelt.de/widerstand-metallschicht-22-0-kohm-0207-0-6-w-1--metall-22-0k-p11622.html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
Widerstände 20 kohm | 20 | | Reichelt | | METALL 20,0K | https://www.reichelt.de/widerstand-metallschicht-20-0-kohm-0207-0-6-w-1--metall-20-0k-p11606.html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
Widerstände 10kohm | 20 | | Reichelt | | METALL 10,0K | https://www.reichelt.de/widerstand-metallschicht-10-0-kohm-0207-0-6-w-1--metall-10-0k-p11449.html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
Widerstände 2kohm | 20 | | Reichelt | | METALL 2,00K | https://www.reichelt.de/widerstand-metallschicht-2-00-kohm-0207-0-6-w-1--metall-2-00k-p11578.html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
Widerstände 1 kohm | 20 | | Reichelt | | METALL 1,00K | https://www.reichelt.de/widerstand-metallschicht-1-00-kohm-0207-0-6-w-1--metall-1-00k-p11403.html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
Widerstände 680 ohm | 20 | | Reichelt | | METALL 680 | https://www.reichelt.de/widerstand-metallschicht-680-ohm-0207-0-6-w-1--metall-680-p11942.html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
Widerstände 10 ohm | 20 | | Reichelt | | METALL 10,0 | https://www.reichelt.de/widerstand-metallschicht-10-0-ohm-0207-0-6-w-1--metall-10-0-p11448.html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
Folienkondensator 1uF | 1 | | Reichelt | | MMK 1,0U 100 | https://www.reichelt.de/folienkondensator-1-0-f-100v-100-c-mmk-1-0u-100-p206627.html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
Elektrolytkondensator 47 uF | 2 | | Reichelt | | RAD LXZ 25/47 | https://www.reichelt.de/elko-radial-47-f-25-v-105-low-esr-5-x-11-5-mm-rm-2-5-rad-lxz-25-47-p166381.html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
Kondensator, 100nF | 20 | | Reichelt | | X7R-5 100N | https://www.reichelt.de/vielschicht-kerko-100-nf-50-100-v-x7r-10-rm-5-0-x7r-5-100n-p22865.html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
Kerko 5.6 nF | 20 | | Reichelt | | KERKO-500 5,6N | https://www.reichelt.de/keramik-kondensator-500v-5-6n-kerko-500-5-6n-p9344.html?&trstct=pol_0&nbc=1
Kerko 2.2 nF | 20 | | Reichelt | | KERKO-500 2,2N | https://www.reichelt.de/kerko-scheibe-2-2-nf-z5u-20-500v-rm-5-08-kerko-500-2-2n-p9325.html?&trstct=pol_2&nbc=1
Kerko 1 nF | 20 | | Reichelt | | KERKO-500 1,0N | https://www.reichelt.de/keramik-kondensator-500v-1-0n-kerko-500-1-0n-p9308.html?&trstct=pos_0&nbc=1
Kerko 680 pF | 20 | | Reichelt | | KERKO-500 680P | https://www.reichelt.de/keramik-kondensator-500v-680p-kerko-500-680p-p9350.html?&trstct=pol_1&nbc=1
Dioden SB140 (Schottky | 5 | | Reichelt | | SB 140 | https://www.reichelt.de/schottkydiode-40-v-1-a-do-41-sb-140-p16024.html
Dioden 1N4148 | 30 | | Reichelt | | 1N 4148 | https://www.reichelt.de/schalt-diode-100-v-150-ma-do-35-1n-4148-p1730.html?&trstct=pos_0&nbc=1
Transistoren BC548 (NPN) | 7 | | Reichelt | | BC 548C | https://www.reichelt.de/de/de/bipolartransistor-npn-30v-0-1a-0-5w-to-92-bc-548c-p5010.html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
2N 3904 Bipolartransistor, NPN | 20 | | Reichelt | | 2N 3904 | https://www.reichelt.de/bipolartransistor-npn-40v-0-2a-0-5w-to-92-2n-3904-p2020.html
J113 (JFET) | 10 | | Reichelt | | J113 | https://www.reichelt.de/n-kanal-jfet-35v-2ma-0-625w-to-92-j113-p273739.html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
Drehpotentiometer, 250 kOhm, linear, 6 mm | 2 | | Reichelt | | PIH PC16IP06254A | https://www.reichelt.de/drehpotentiometer-250-kohm-linear-6-mm-pih-pc16ip06254a-p232706.html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
Potentiometer 100k (vertical) | 5 | | Reichelt | | RK09K113-LIN100K | https://www.reichelt.de/drehpotentiometer-mono-100-kohm-linear-6-mm-rk09k113-lin100k-p73818.html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
ICs TL074 | 5 | | Reichelt | | TL 074 DIL | https://www.reichelt.de/operationsverstaerker-4-fach-dip-14-tl-074-dil-p21557.html
ICs TL 072 | 5 | | | | TL 072 ACP | https://www.reichelt.de/de/de/operationsverstaerker-2-fach-dip-8-tl-072-acp-p189107.html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

Envelope Generator
ICs TL074 | 5 | | Reichelt | | TL 074 DIL | https://www.reichelt.de/operationsverstaerker-4-fach-dip-14-tl-074-dil-p21557.html
Widerstände 100 kohm | 10 | | Reichelt | | METALL 100K | https://www.reichelt.de/widerstand-metallschicht-100-kohm-0207-0-6-w-1--metall-100k-p11458.html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
Widerstände 47 kohm | 20 | | Reichelt | | METALL 47,0K | https://www.reichelt.de/widerstand-metallschicht-47-0-kohm-0207-0-6-w-1--metall-47-0k-p11823.html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
Widerstände 1 kohm | 20 | | Reichelt | | METALL 1,00K | https://www.reichelt.de/widerstand-metallschicht-1-00-kohm-0207-0-6-w-1--metall-1-00k-p11403.html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
Widerstände 10kohm | 20 | | Reichelt | | METALL 10,0K | https://www.reichelt.de/widerstand-metallschicht-10-0-kohm-0207-0-6-w-1--metall-10-0k-p11449.html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
Potentiometer 100k (vertical) | 5 | | Reichelt | | RK09K113-LIN100K | https://www.reichelt.de/drehpotentiometer-mono-100-kohm-linear-6-mm-rk09k113-lin100k-p73818.html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
potentiometer 1 Mohm
Dioden 1N4148 | 30 | | Reichelt | | 1N 4148 | https://www.reichelt.de/schalt-diode-100-v-150-ma-do-35-1n-4148-p1730.html?&trstct=pos_0&nbc=1
1 uF Kondensator | 6 | | Reichelt | | T356 1,0U 35 | https://www.reichelt.de/tantal-bedrahtet-1-0-f-35v-85-c-t356-1-0u-35-p206422.html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
Widerstände 2kohm | 20 | | Reichelt | | METALL 2,00K | https://www.reichelt.de/widerstand-metallschicht-2-00-kohm-0207-0-6-w-1--metall-2-00k-p11578.html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

Output
Widerstände 10 ohm | 10 | | Reichelt | | METALL 10,0 | https://www.reichelt.de/widerstand-metallschicht-10-0-ohm-0207-0-6-w-1--metall-10-0-p11448.html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
Elektrolytkondensator 47 uF | 2 | | Reichelt | | RAD LXZ 25/47 | https://www.reichelt.de/elko-radial-47-f-25-v-105-low-esr-5-x-11-5-mm-rm-2-5-rad-lxz-25-47-p166381.html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
Kondensator, 100nF | 20 | | Reichelt | | X7R-5 100N | https://www.reichelt.de/vielschicht-kerko-100-nf-50-100-v-x7r-10-rm-5-0-x7r-5-100n-p22865.html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
Dioden 1N4148 | 30 | | Reichelt | | 1N 4148 | https://www.reichelt.de/schalt-diode-100-v-150-ma-do-35-1n-4148-p1730.html?&trstct=pos_0&nbc=1
ICs TL 072 | 5 | | | | TL 072 ACP | https://www.reichelt.de/de/de/operationsverstaerker-2-fach-dip-8-tl-072-acp-p189107.html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
Keramik-Kondensator, 22 pF | 7 | | | | KERKO-500 22P | https://www.reichelt.de/keramik-kondensator-22-pf-10-npo-500-v-rm-5-kerko-500-22p-p9330.html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
Widerstände 100kohm | 20 | | Reichelt | | METALL 100K | https://www.reichelt.de/widerstand-metallschicht-100-kohm-0207-0-6-w-1--metall-100k-p11458.html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
Widerstände 10kohm | 20 | | Reichelt | | METALL 10,0K | https://www.reichelt.de/widerstand-metallschicht-10-0-kohm-0207-0-6-w-1--metall-10-0k-p11449.html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
Widerstände 1 kohm | 20 | | Reichelt | | METALL 1,00K | https://www.reichelt.de/widerstand-metallschicht-1-00-kohm-0207-0-6-w-1--metall-1-00k-p11403.html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
Widerstände 3.6 kohm | 20 | | Reichelt | | METALL 3,60K | https://www.reichelt.de/widerstand-metallschicht-3-60-kohm-0207-0-6-w-1--metall-3-60k-p11700.html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
| | | | | | VCF
Widerstände 100kohm | 10 | Reichelt | | METALL 100K | | | https://www.reichelt.de/widerstand-metallschicht-100-kohm-0207-0-6-w-1--metall-100k-p11458.html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
Widerstände 3Mohm | 5 | Reichelt | | MF0207FTE52-3M | | | https://www.reichelt.de/widerstand-metallschicht-3-0-mohm-0207-0-6-w-1--metall-3-00m-p11687.html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
Widerstände 10kohm | 5 | Reichelt | | METALL 10K | | | https://www.reichelt.de/widerstand-metallschicht-10-0-kohm-0207-0-6-w-1--metall-10-0k-p11449.html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
Widerstände 1 kohm | 2 | Reichelt | | METALL 1,00K | | | https://www.reichelt.de/widerstand-metallschicht-1-00-kohm-0207-0-6-w-1--metall-1-00k-p11403.html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
Kondensatoren Folienkondensator 2.2 nF | 5 | CONRAD | | 1589394 - NA | | | https://www.conrad.de/de/p/tru-components-tc-k2-2nf500v-keramik-kondensator-tht-2-2-nf-500-v-20-1-st-1589394.html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
Potentiometer 100k | 3 | Reichelt | | RK09K113-LIN100K | | | https://www.reichelt.de/drehpotentiometer-mono-100-kohm-linear-6-mm-rk09k113-lin100k-p73818.html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
Klinkenbuchsen 90 Grad | 4 | Reichelt | | EBS 35 | | | https://www.reichelt.de/klinkeneinbaubuchse-3-5-mm-stereo-ebs-35-p7301.html?&trstct=pos_1&nbc=1
ICs TL074 | 3 | Reichelt | | TL 074 DIL | | | https://www.reichelt.de/operationsverstaerker-4-fach-dip-14-tl-074-dil-p21557.html
Potentiometer 10k | 2 | Reichelt | | 64Y-10K | | | https://www.reichelt.de/praezisionspotentiometer-25-gaenge-stehend-10-kohm-64y-10k-p2716.html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
JFET N-Channel | 5 | Mouser | | PN4391 | | | https://www.mouser.de/ProductDetail/Central-Semiconductor/PN4391-PBFREE?qs=OlC7AqGiEDn2JuUMNczp2g%3D%3D
JFET N-Channel | 2 | Reichelt | | 2SK 161 | | | https://www.reichelt.de/jfet-n-ch-18v-10ma-0-2w-2-4e1d-2sk-161-p2156.html?&trstct=pos_0&nbc=1
Widerstände 4.7 Mohm | 5 | Reichelt | | MF0207FTE52-4M7 | | | https://www.reichelt.de/widerstand-metallschicht-4-7-mohm-0207-0-6-w-1--metall-4-70m-p11785.html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
Cliff CL170825BR Drehknopf Schwarz, Grau (Ø x H) 16.8 mm x 14.5 mm | 10 | conrad | | 548311 | | | https://www.conrad.de/de/p/cliff-cl170825br-drehknopf-schwarz-grau-x-h-16-8-mm-x-14-5-mm-1-st-548311.html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
Cliff CL170823BR Drehknopf Schwarz, Rot (Ø x H) 16.8 mm x 14.5 mm | 10 | conrad | | 704639 | | | https://www.conrad.de/de/p/cliff-cl170823br-drehknopf-schwarz-rot-x-h-16-8-mm-x-14-5-mm-1-st-704639.html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
Cliff CL170827BR Drehknopf Schwarz, Blau (Ø x H) 16.8 mm x 14.5 mm | 10 | | | 704662 | | | https://www.conrad.de/de/p/cliff-cl170827br-drehknopf-schwarz-blau-x-h-16-8-mm-x-14-5-mm-1-st-704662.html
Cliff CL170828BR Drehknopf Schwarz, Grün (Ø x H) 16.8 mm x 14.5 mm | 10 | conrad | | 548312 | | | https://www.conrad.de/de/p/cliff-cl170828br-drehknopf-schwarz-gruen-x-h-16-8-mm-x-14-5-mm-1-st-548312.html
Cliff CL170822BR Drehknopf Schwarz, Weiß (Ø x H) 16.8 mm x 14.5 mm | 10 | conrad | | 548303 | | | https://www.conrad.de/de/p/cliff-cl170822br-drehknopf-schwarz-weiss-x-h-16-8-mm-x-14-5-mm-1-st-548303.html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
