tsedlmeier/Synthesizer/Sonstiges/Synth_Kontakte_Thema.pdf

## Kontakte

Name | E-Mail | Matrikelnummer
Balbach, Thomas | balbachth74629@th-nuernberg.de | 3229936
Kirschner, Christoph | kirschnerch75182@th-nuernberg.de | 3248161
Dilman, Viktor | dilmanvi74631@th-nuernberg.de | 3229955
Sedlmeier, Toni | sedlmeierto75189@th-nuernberg.de | 3236272
Altaher, Ahmad | altaherah90346@th-nuernberg.de | 3654079

## Thema

Entwicklung eines modularen Synthesizers
