tsedlmeier/Synthesizer/Ausarbeitung/src/figures/poti_sweep.png

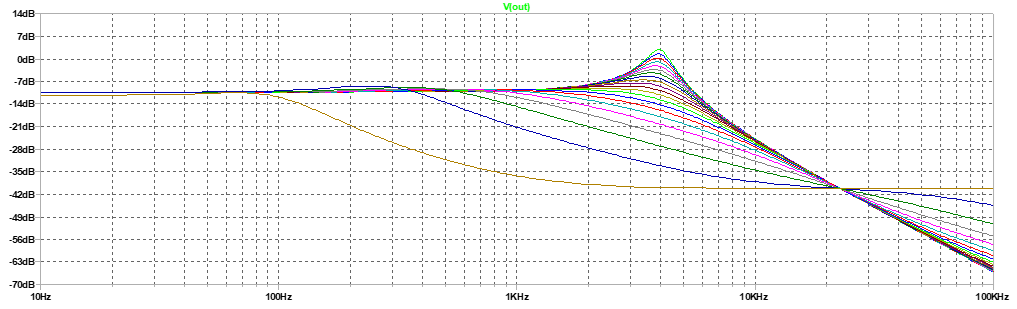
Ausarbeitung/src/figures/poti_sweep.png
