tsedlmeier/Synthesizer/Ausarbeitung/src/figures/SchaltplanMixer.png

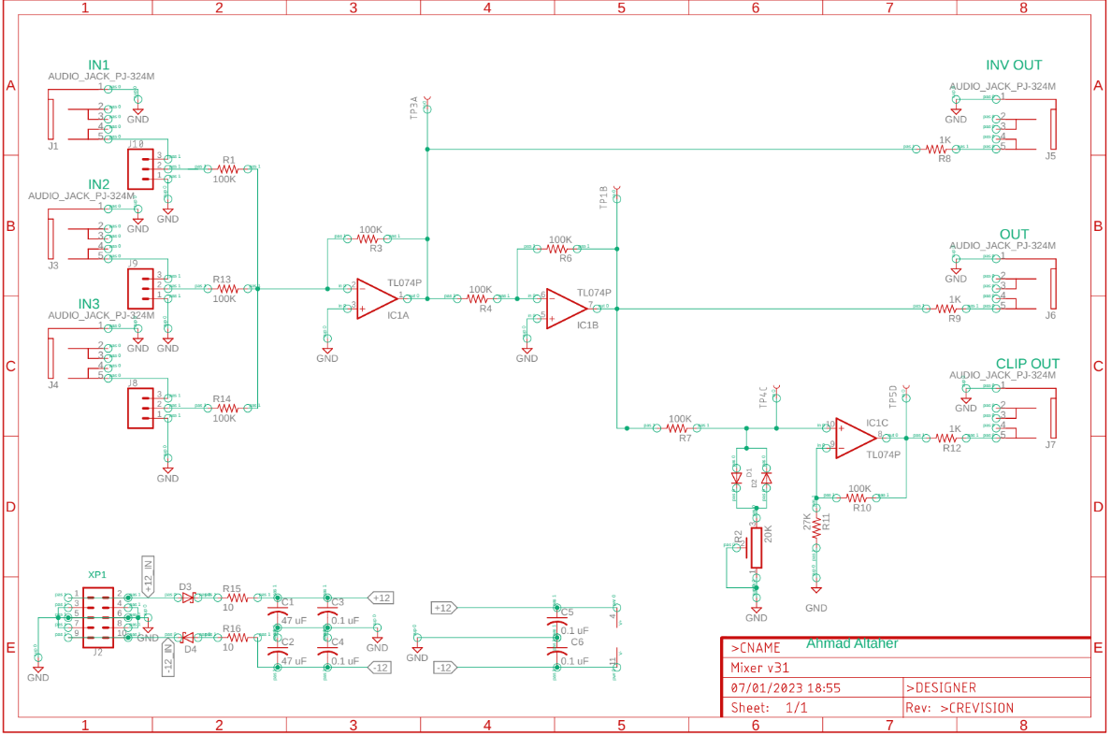
Ausarbeitung/src/figures/SchaltplanMixer.png
