tsedlmeier/Synthesizer/Ausarbeitung/src/figures/VCO_Frontplatte_oben.png

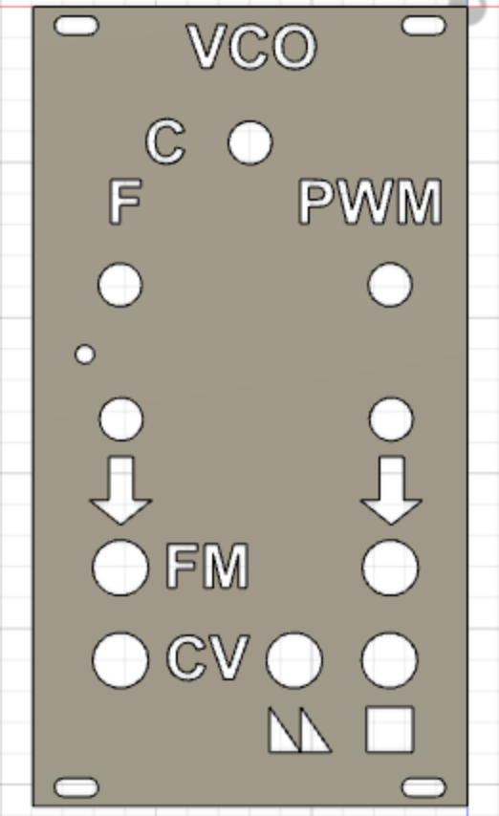
Ausarbeitung/src/figures/VCO_Frontplatte_oben.png
