tsedlmeier/Synthesizer/Mixer/Mixer _schaltplan _2.14.23 (1).png

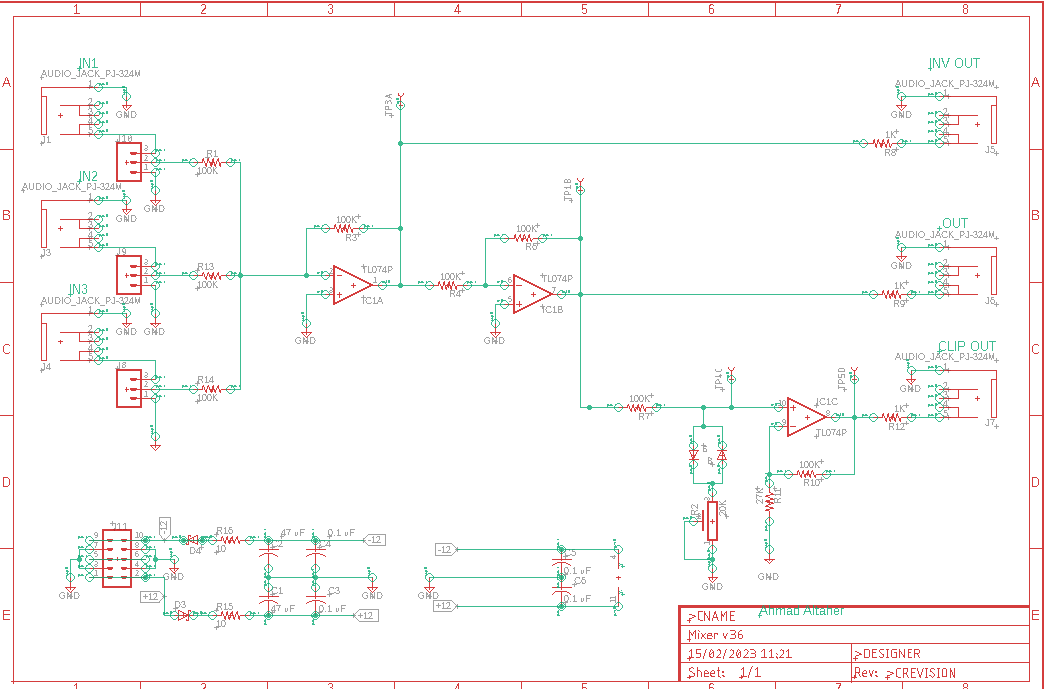
Mixer/Mixer _schaltplan _2.14.23 (1).png
