tsedlmeier/Synthesizer/Mixer/Mixer _schaltplan _2.14.23 (2).png

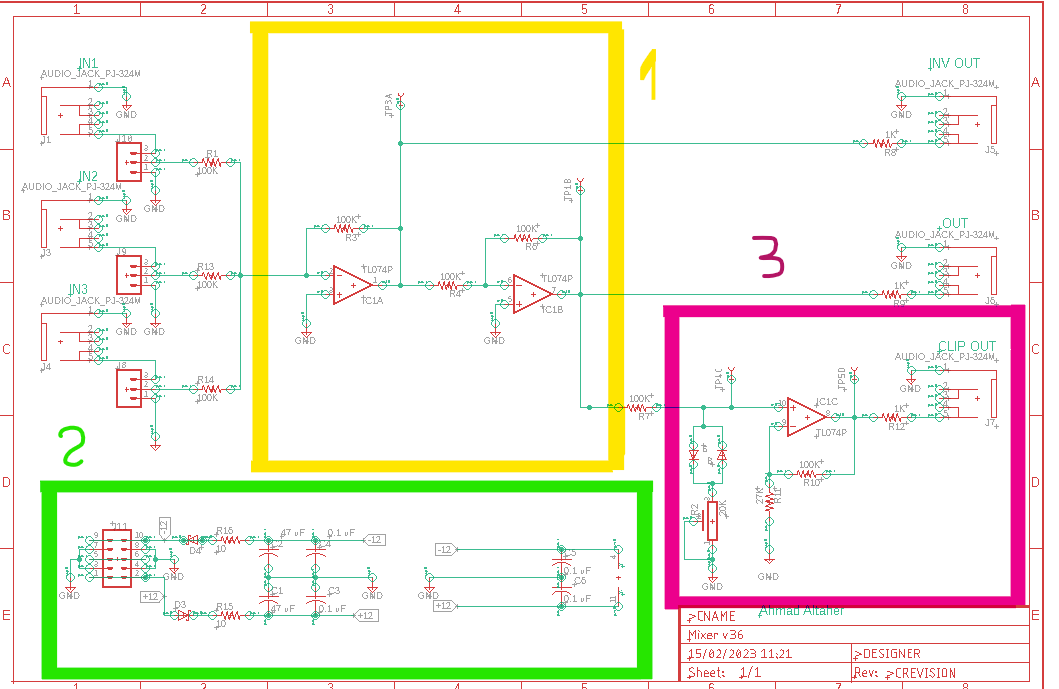
Mixer/Mixer _schaltplan _2.14.23 (2).png
