tsedlmeier/Synthesizer/Mixer/mixer layout _2.15.23.png

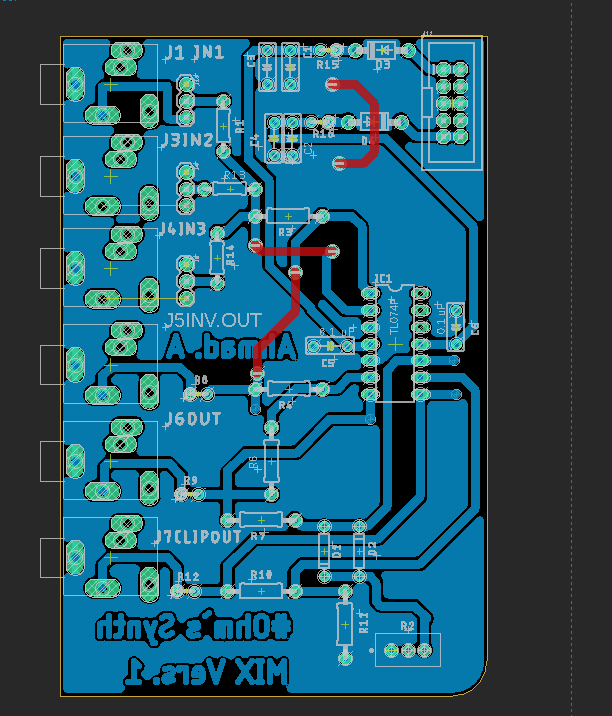
Mixer/mixer layout _2.15.23.png
