tsedlmeier/Synthesizer/Sonstiges/Export_Gerber.PNG

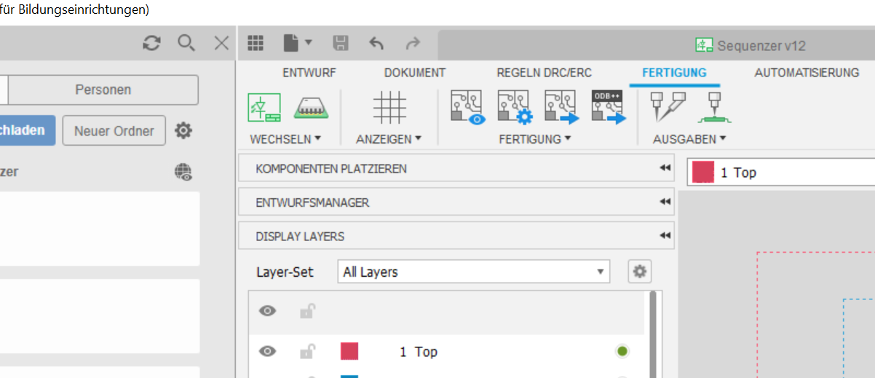
Sonstiges/Export_Gerber.PNG
