tsedlmeier/Synthesizer/Sonstiges/IMG-20221122-WA0002.jpg

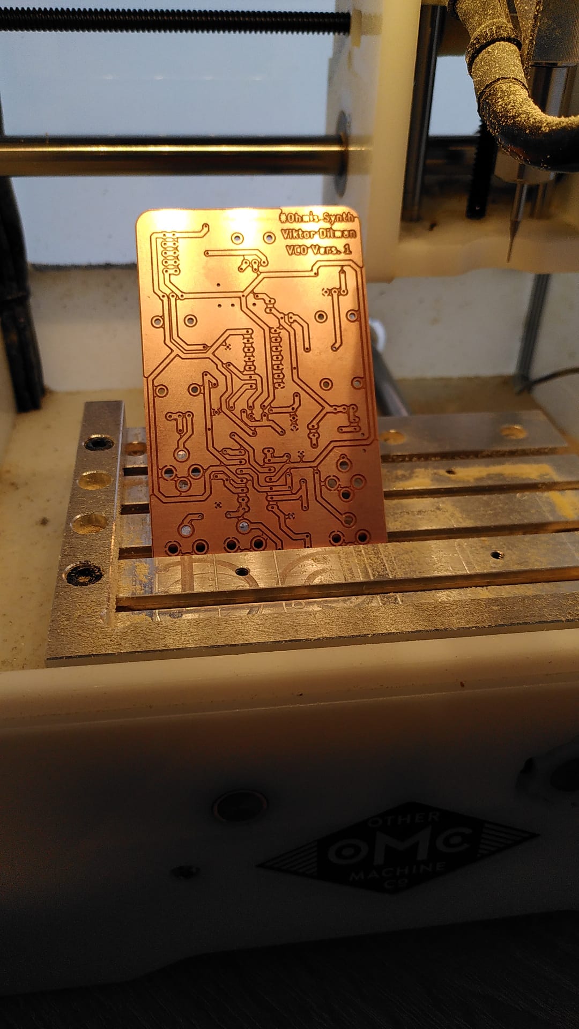
Sonstiges/IMG-20221122-WA0002.jpg
