tsedlmeier/Synthesizer/Sonstiges/SEQ.PNG

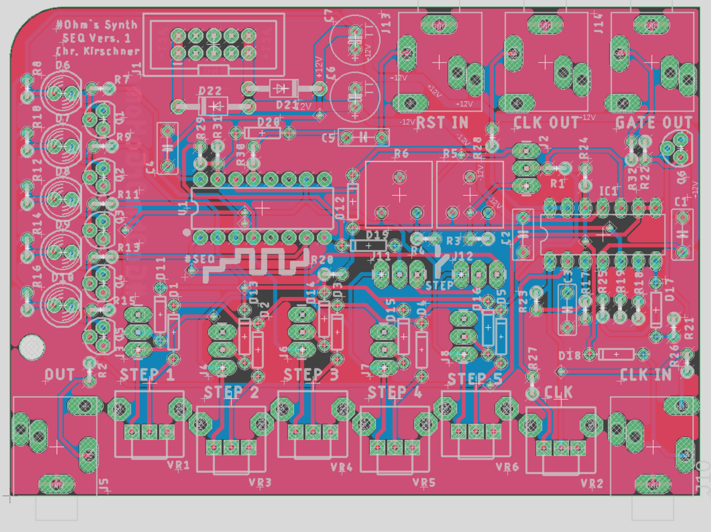
Sonstiges/SEQ.PNG
