tsedlmeier/Synthesizer/VCF/vcf_R_50_poti_100.PNG

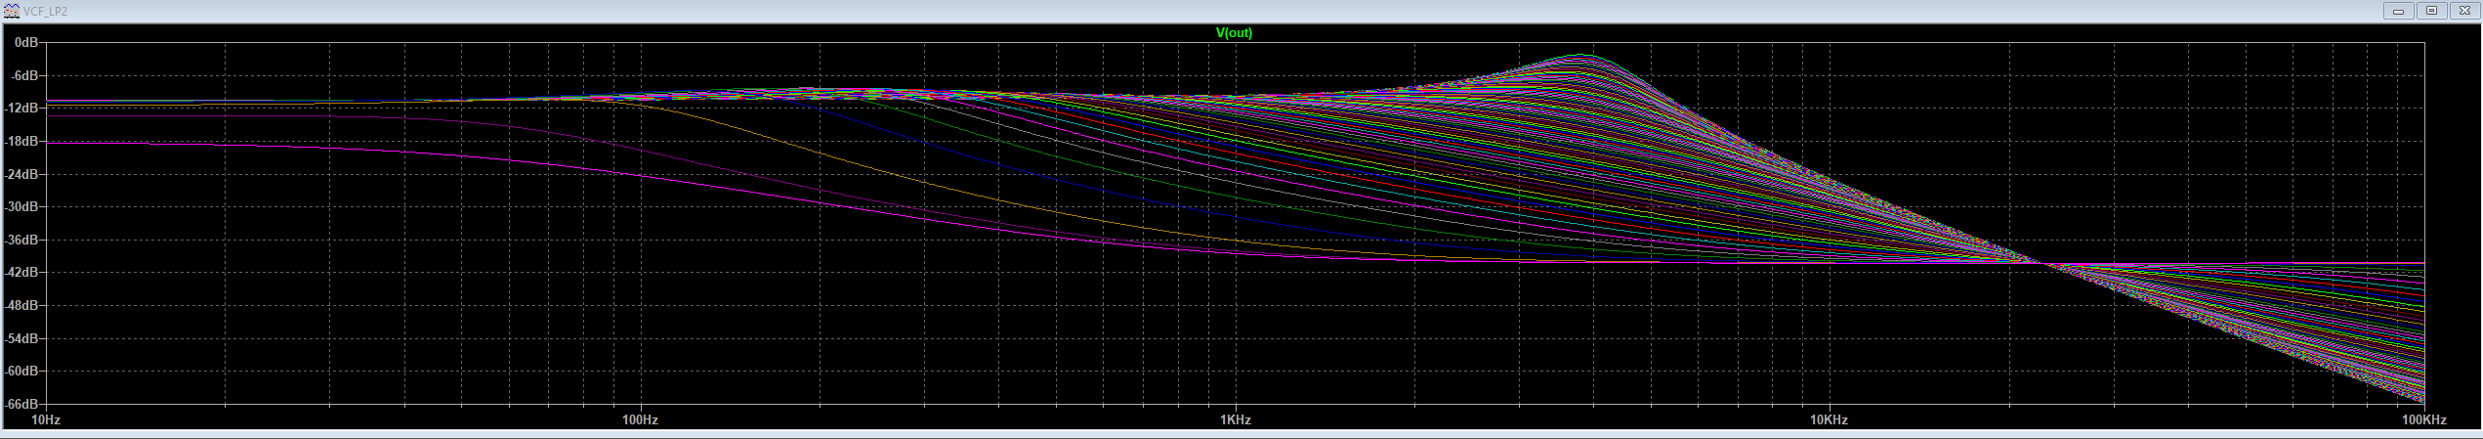
VCF/vcf_R_50_poti_100.PNG
