tsedlmeier/Synthesizer/SEQ/Schaltplan_Sequenzer_Christoph_Kirschner_12_12_22.pdf

0.1u 1N⁴¹⁴⁸ | 100kGND | 1nF
47u GND | 100k

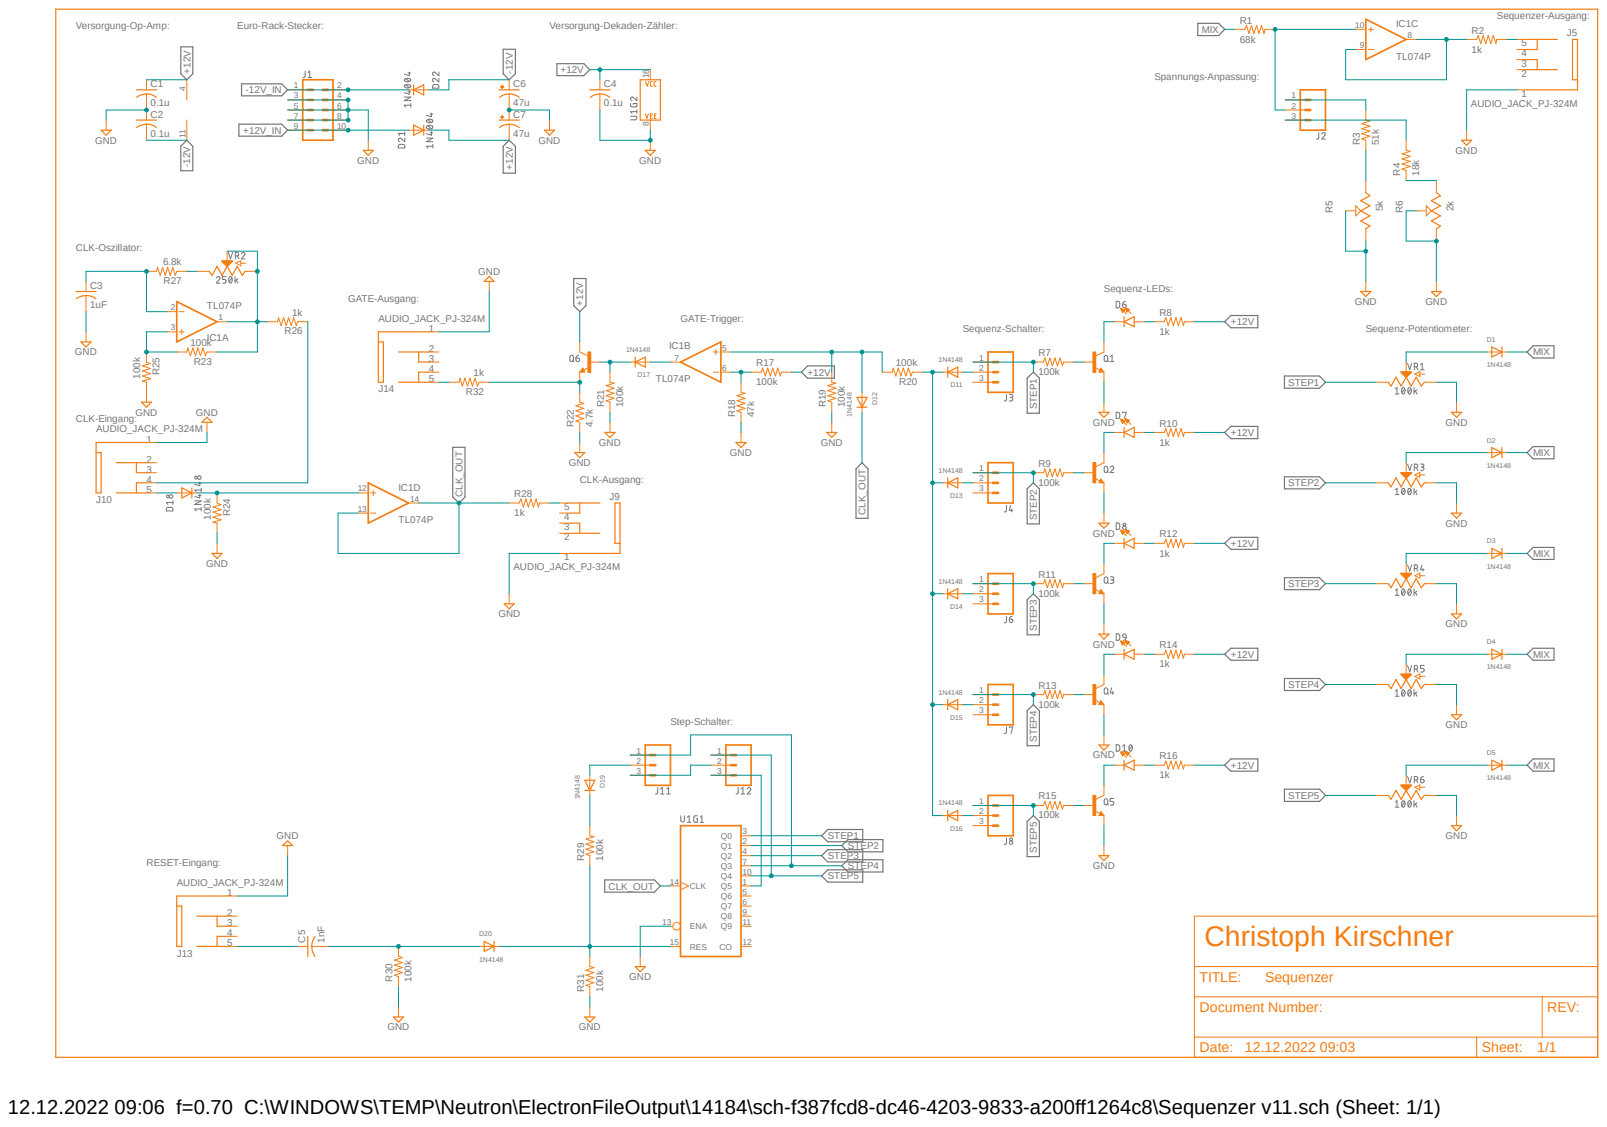
[picture p97: page 1]

Document Number: | REV:

Date: 12.12.2022 09:03 | Sheet: 1/1

12.12.2022 09:06 f=0.70 C:\WINDOWS\TEMP\Neutron\ElectronFileOutput\14184\sch-f387fcd8-dc46-4203-9833-a200ff1264c8\Sequenzer v11.sch (Sheet: 1/1)
