tsedlmeier/Synthesizer/VCF/Schaltplan_VCF_v4_22.11.2022.pdf

-12V -12V

+12V +12V

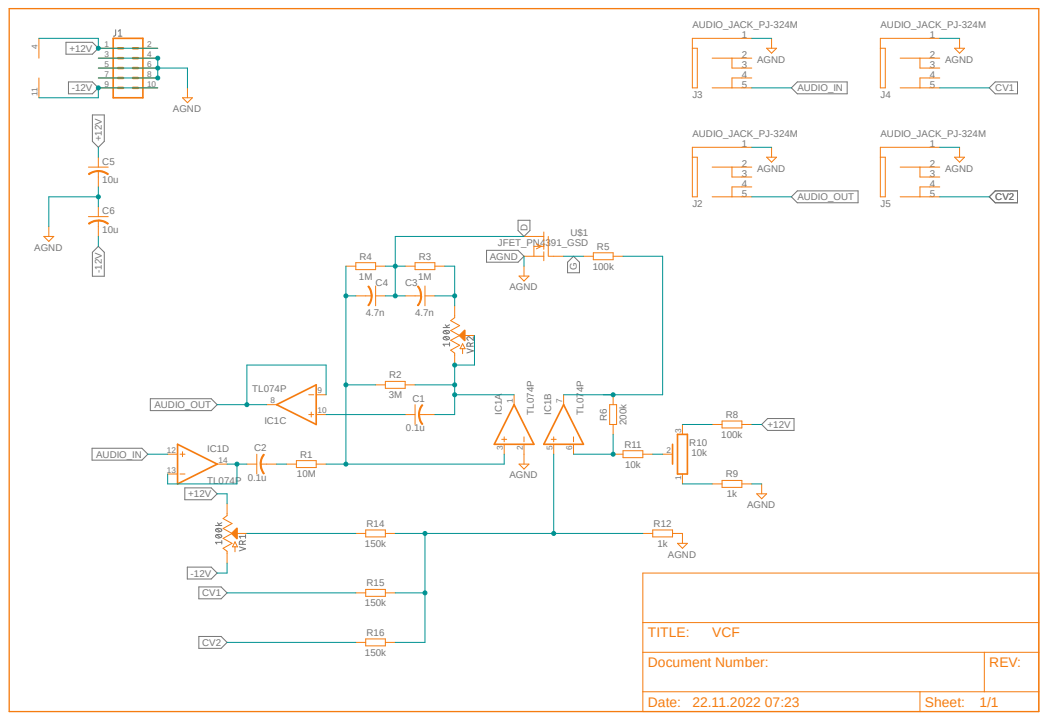
[picture p98: page 1]

Document Number: | REV:

Date: 22.11.2022 07:23 | Sheet: 1/1
