tsedlmeier/Synthesizer/SEQ/Schaltplan_Sequenzer_Christoph_Kirschner_09_11_22.pdf

0.1u 1N⁴¹⁴⁸ | 100kGND | 1nF
47u GND | 100k

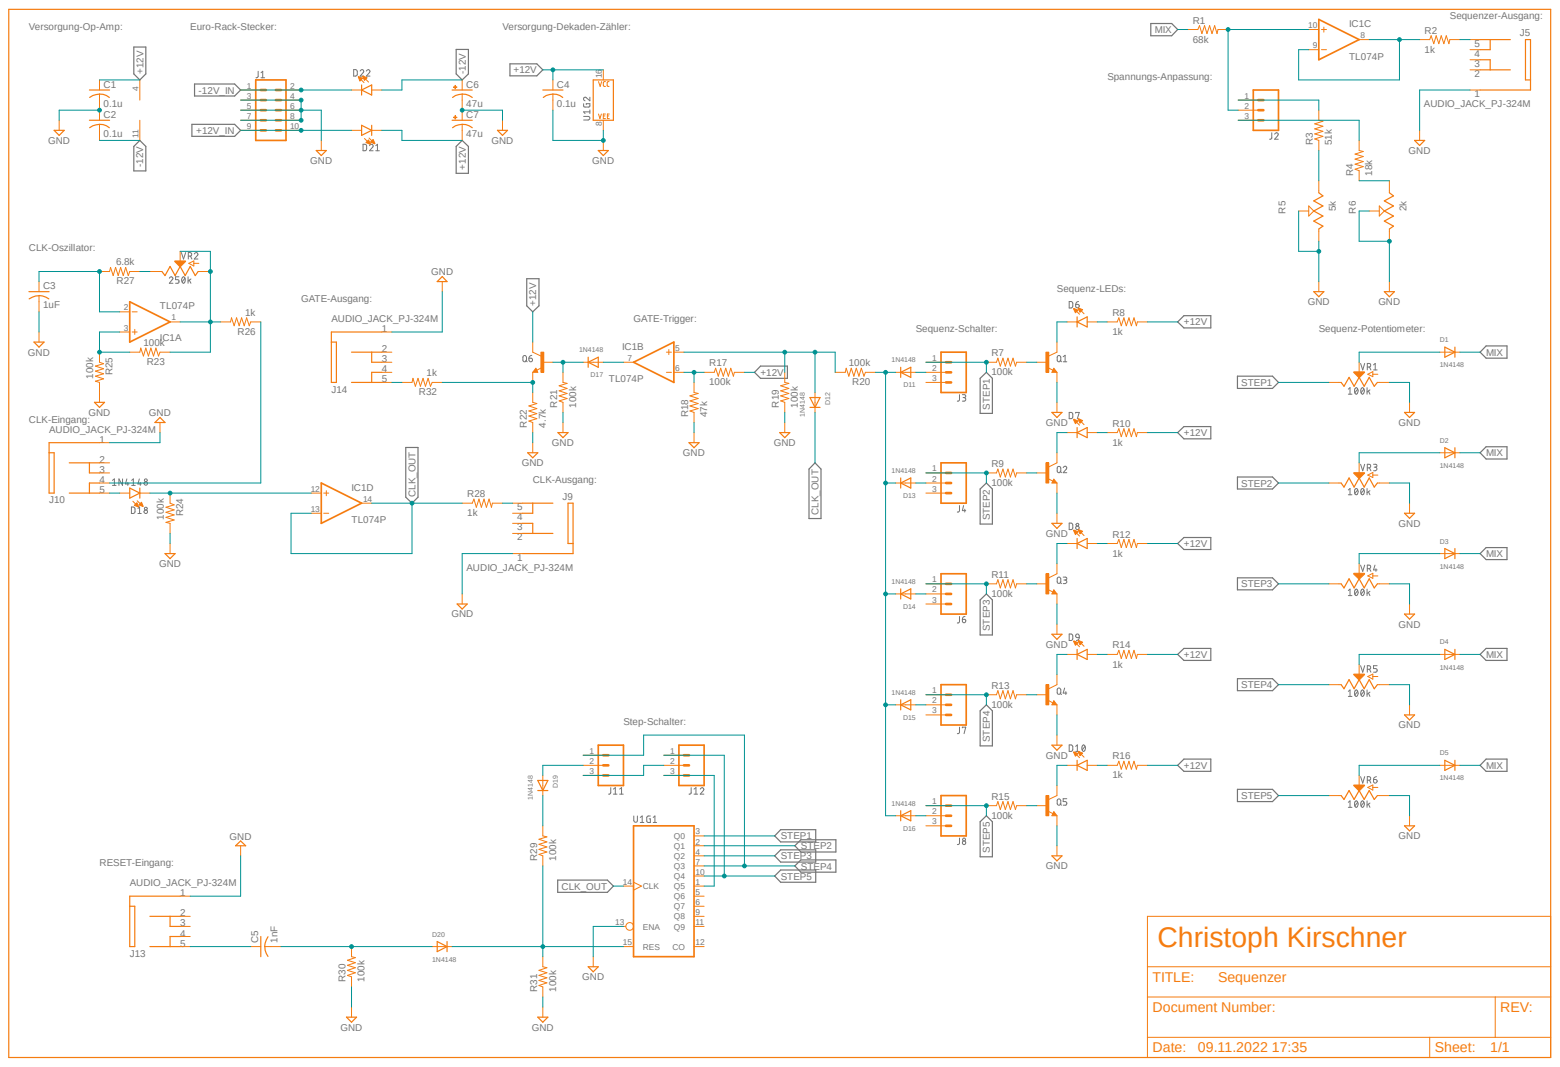
[picture p99: page 1]

Document Number: | REV:

Date: 09.11.2022 17:35 | Sheet: 1/1
