tsedlmeier/Synthesizer/VCO/VCO_v3/VCO_v3_Stromlaufplan_v52.pdf

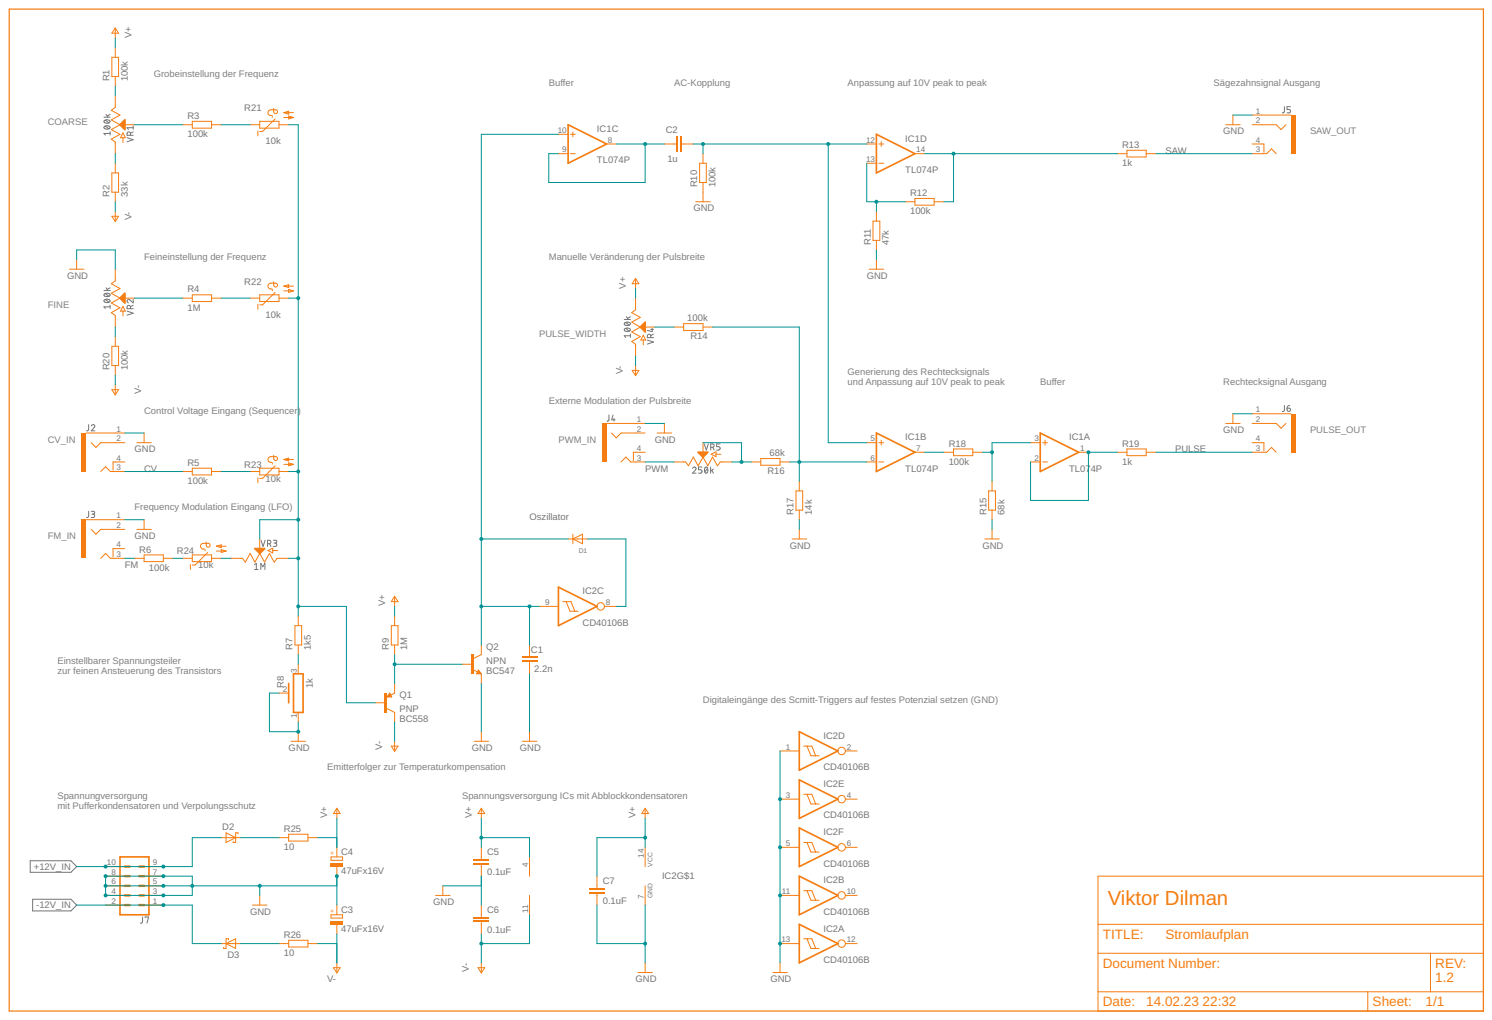
[picture p100: page 1]

Anpassung auf 10V peak to peak

Manuelle Veränderung der Pulsbreite

Buffer Generierung des Rechtecksignals und Anpassung auf 10V peak to peak

Control Voltage Eingang (Sequencer)

Einstellbarer Spannungsteiler zur feinen Ansteuerung des Transistors

Digitaleingänge des Scmitt-Triggers auf festes Potenzial setzen (GND)

4 | 3 | V-

Stromlaufplan Date: Sheet: | REV: TITLE: Document Number: 1.2
