tsedlmeier/Synthesizer/VCF/Layout_VCF_v4_22.11.2022.pdf

J4

# R16 R²

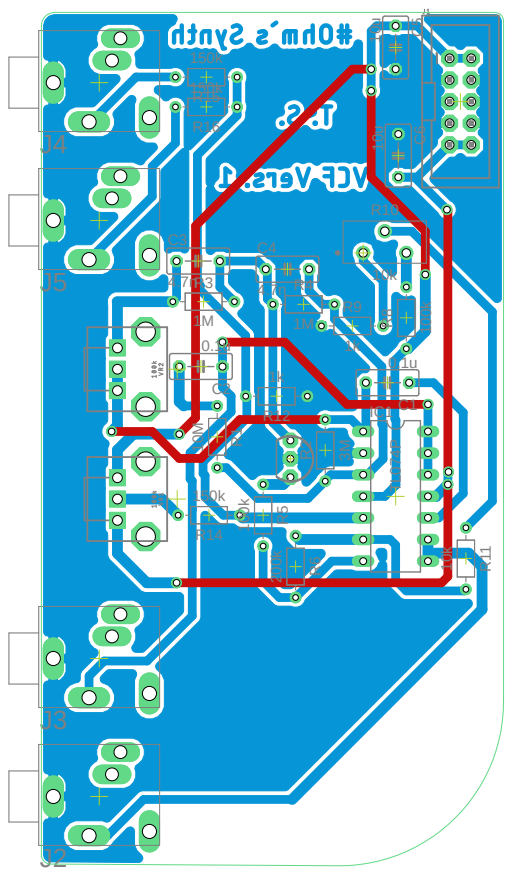
[picture p105: page 1]
