tsedlmeier/Synthesizer/LFO/Schaltplan_LFO_Kirschner_09_11_22.pdf

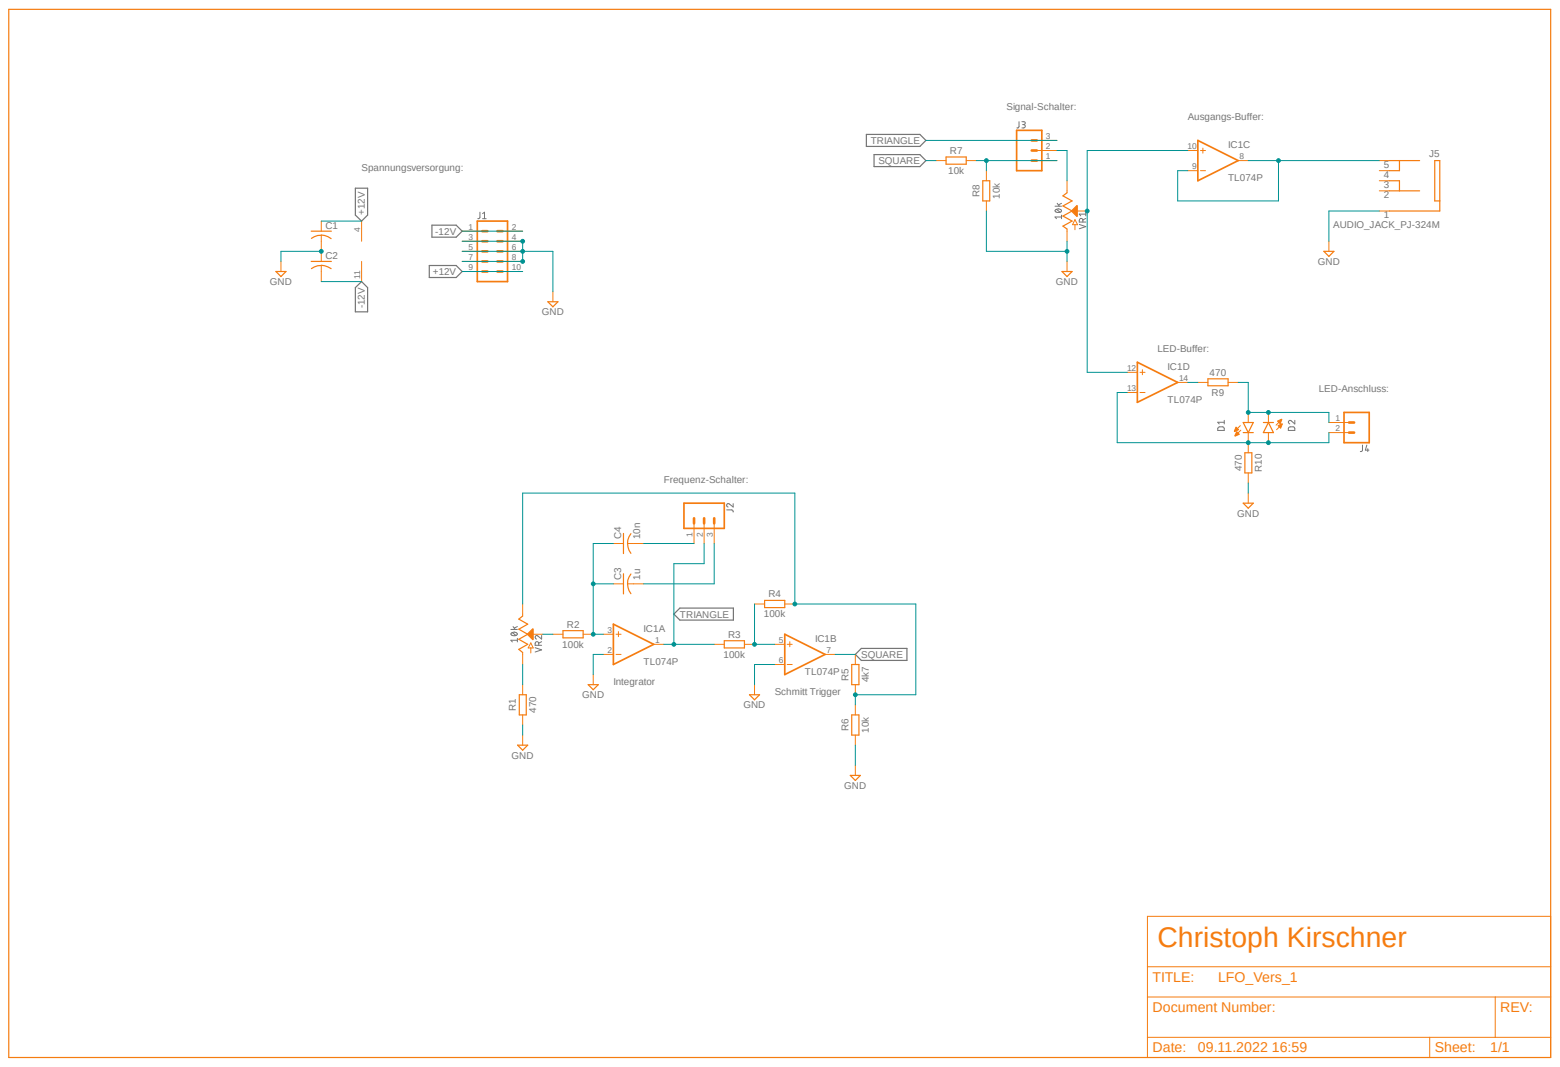
[picture p106: page 1]

Document Number: | REV:

Date: 09.11.2022 16:59 | Sheet: 1/1
