tsedlmeier/Synthesizer/Mixer/DokumentationMixer/Schaltplan.pdf

1

2

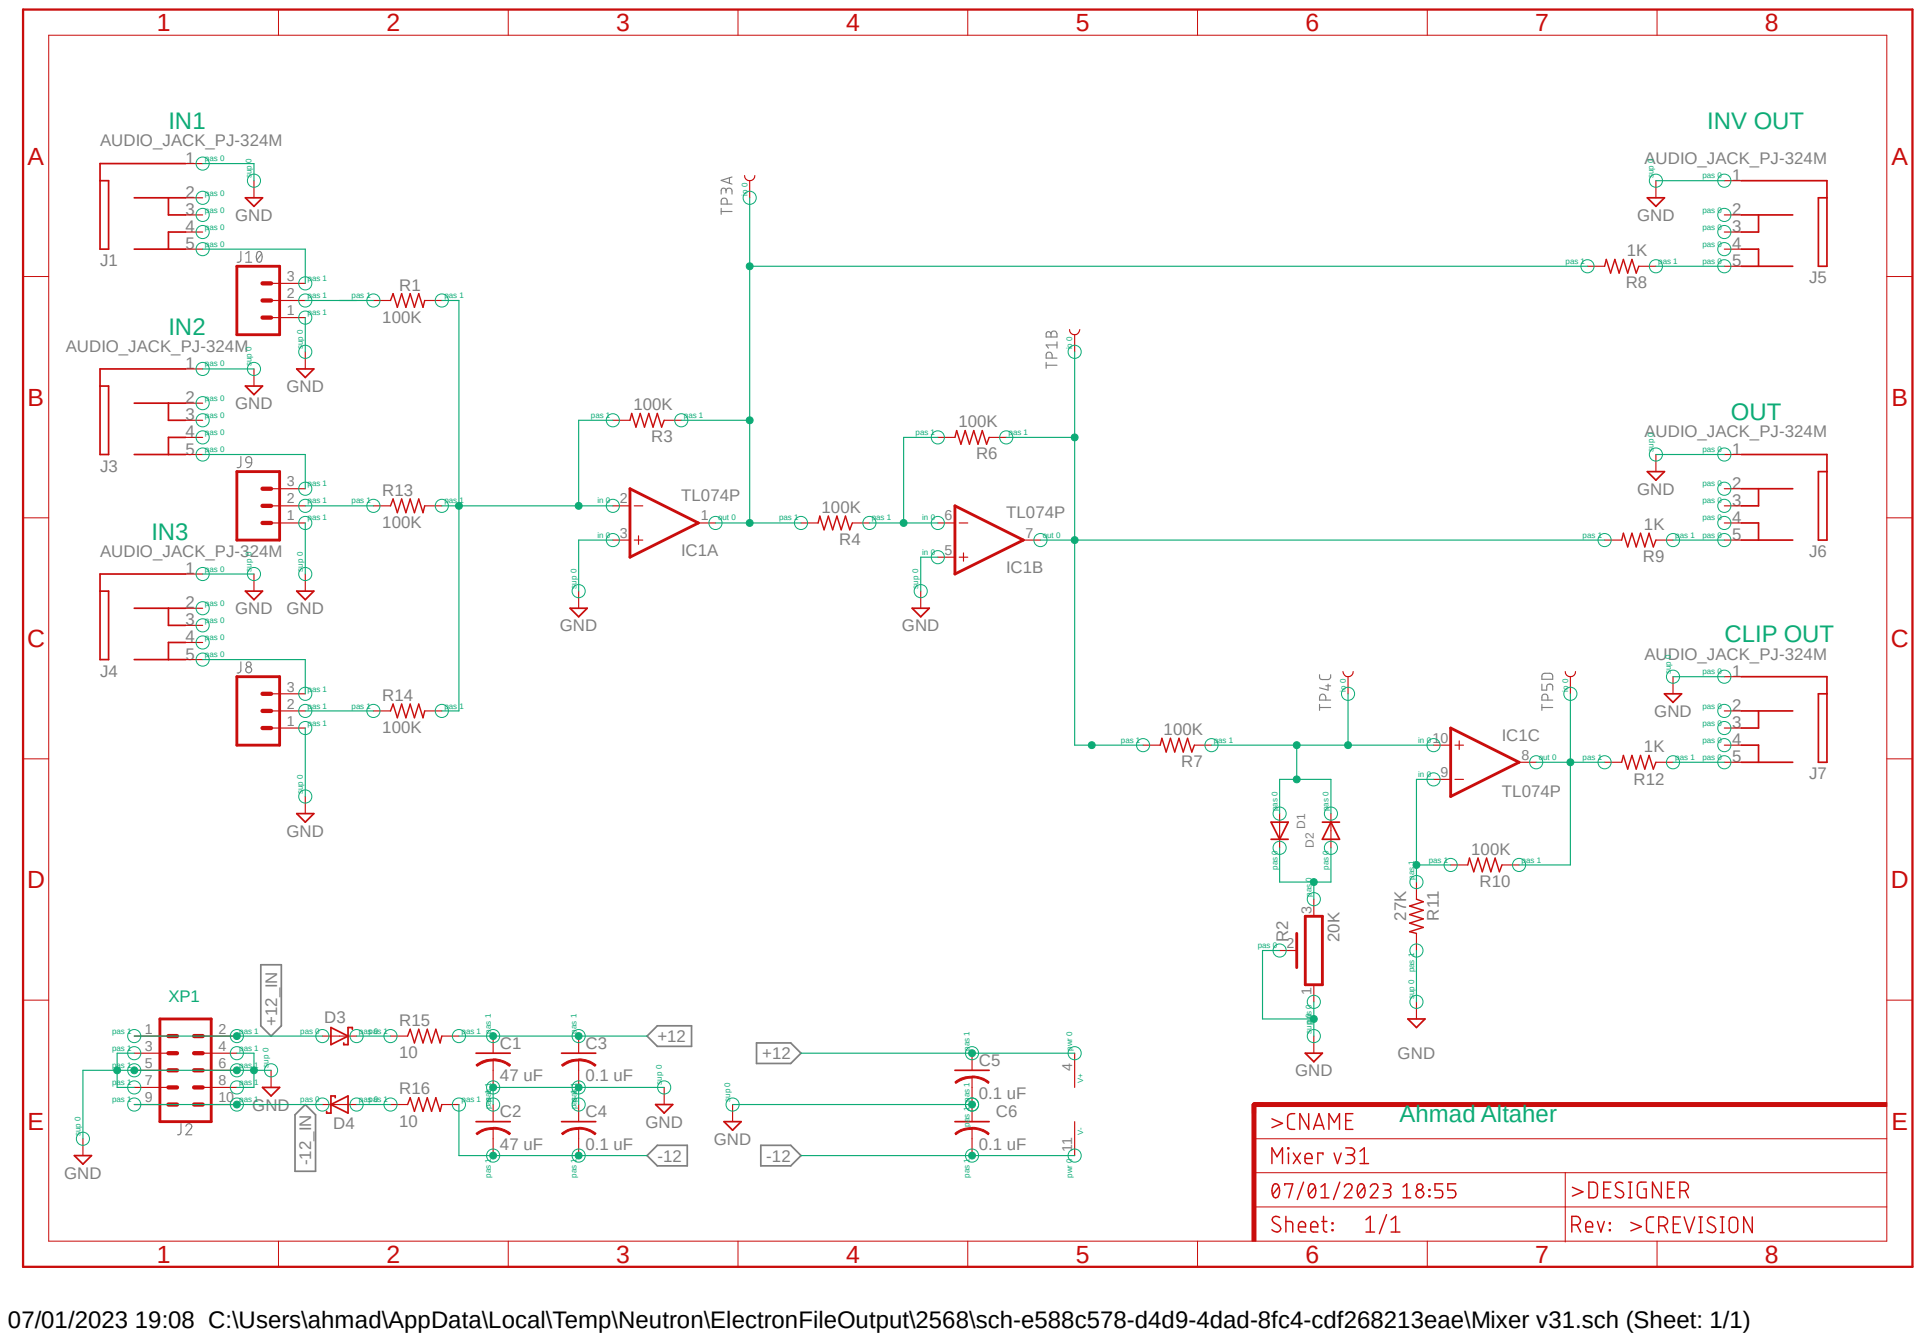
[picture p107: page 1]

pas 0 io 0 sup 0 sup 0 sup 0 sup 0 sup 0

07/01/2023 19:08 C:\Users\ahmad\AppData\Local\Temp\Neutron\ElectronFileOutput\2568\sch-e588c578-d4d9-4dad-8fc4-cdf268213eae\Mixer v31.sch (Sheet: 1/1)
