tsedlmeier/Synthesizer/VCO/VCO_v3/Leiterplatte v67.pdf

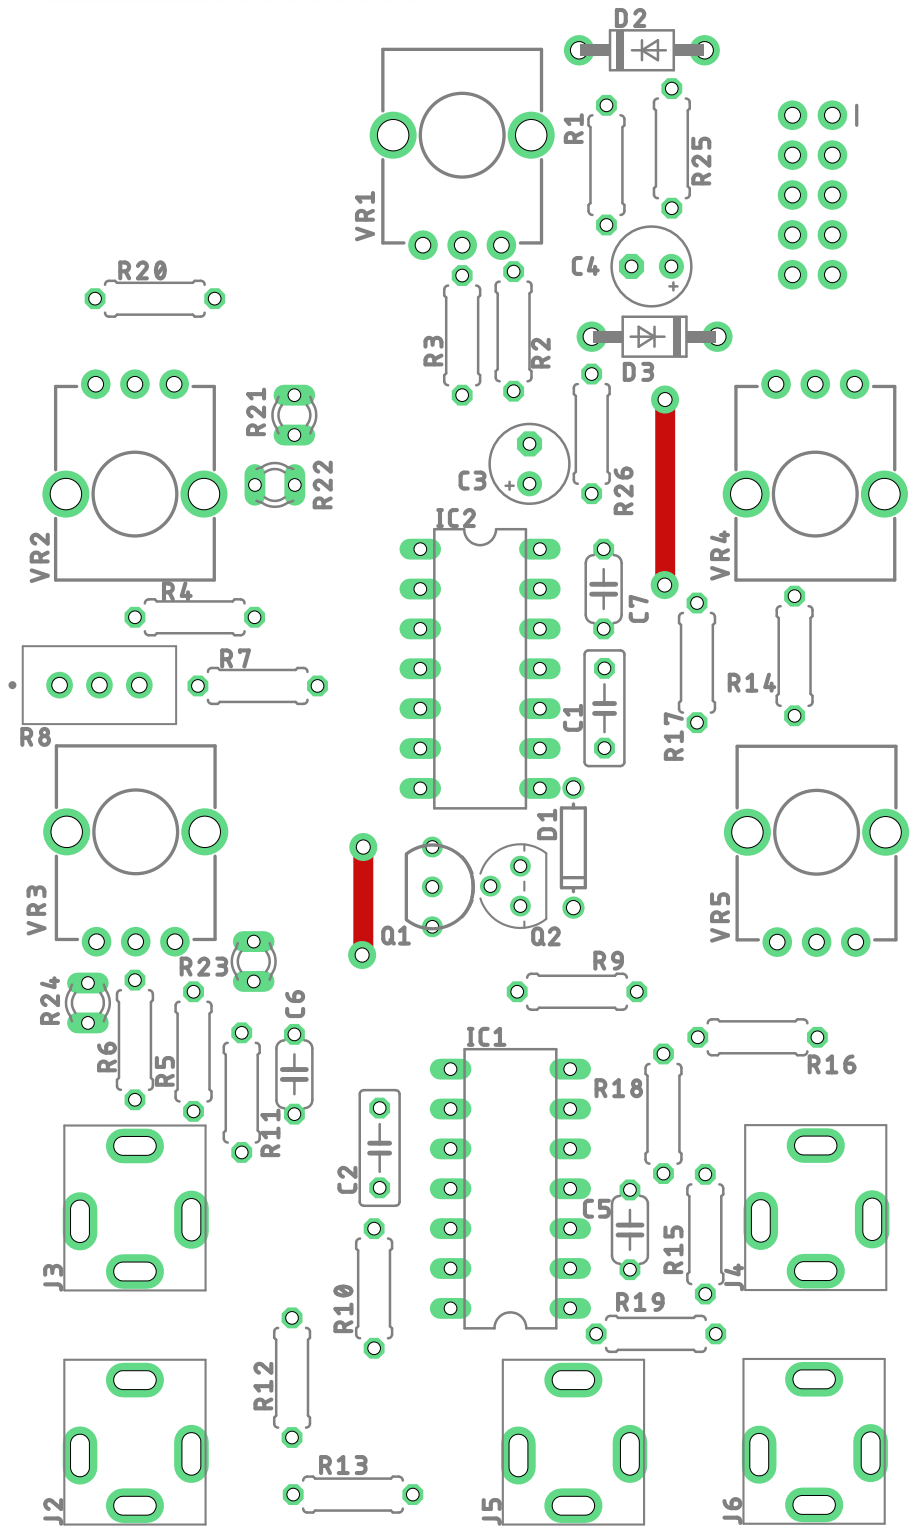
[picture p108: page 1]
