tsedlmeier/Synthesizer/Ausarbeitung/src/figures/Schaltplan_Sequenzer_Christoph_Kirschner_unterteilt.pdf

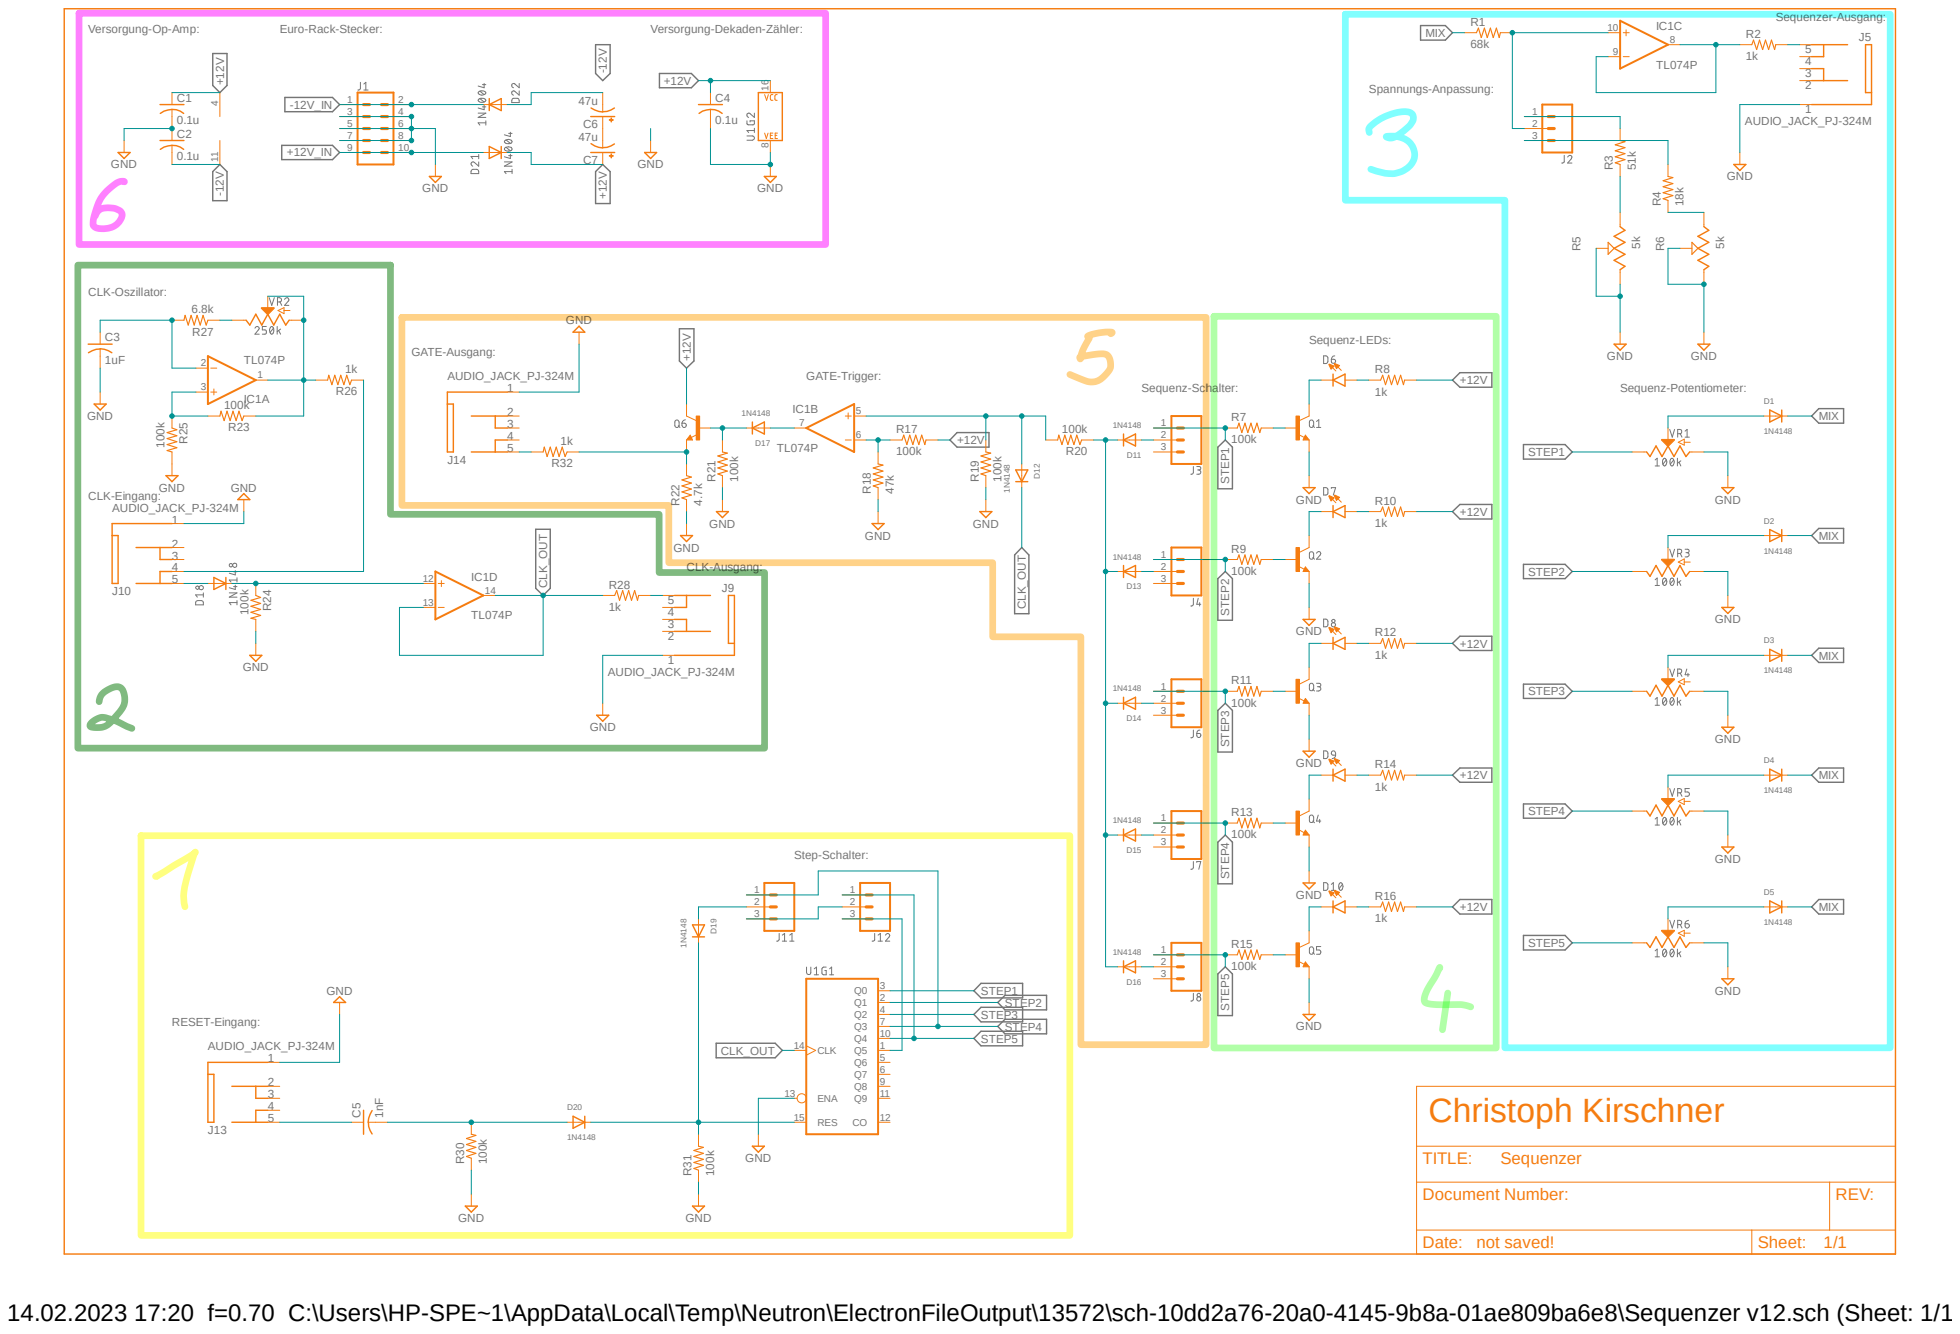
[picture p109: page 1]

Document Number: | REV:

Date: not saved! | Sheet: 1/1

14.02.2023 17:20 f=0.70 C:\Users\HP-SPE~1\AppData\Local\Temp\Neutron\ElectronFileOutput\13572\sch-10dd2a76-20a0-4145-9b8a-01ae809ba6e8\Sequenzer v12.sch (Sheet: 1/1)
