tsedlmeier/Synthesizer/LTSpice/VCF/Draft1.asc

C1: cap; 4.7n
C2: cap; 4.7n
C3: cap; 0.1µ
C4: cap; 0.1µ
C5: cap; 4.7n
C6: cap; 4.7n
C7: cap; 0.1µ
C8: cap; 0.1µ
J1: njf; PN4391
J2: njf; PN4391
R1: res; 10Meg
R2: res; 3Meg
R3: res; 1Meg
R4: res; 1Meg
R5: res; 100k
R6: res; 100k
R7: res; 200k
R8: res; 1k
R9: res; 10k
R10: res; 100k
R11: res; 1k
R12: res; 150k
R13: res; 150k
R14: res; 100k
R15: res; {R}
R16: res; 50k
R17: res; 2k
R18: res; 8k
R19: res; 10k
R20: res; 10Meg
R21: res; 3Meg
R22: res; 1Meg
R23: res; 1Meg
R24: res; 100k
R25: res; 100k
R26: res; 200k
R27: res; 1k
R28: res; 10k
R29: res; 100k
R30: res; 1k
R31: res; 150k
R32: res; 150k
R33: res; 100k
R34: res; {R}
R35: res; 50k
R36: res; 2k
R37: res; 8k
R38: res; 10k
U1: LMX58B_LM2904B
U2: LMX58B_LM2904B
U3: LMX58B_LM2904B
U4: LMX58B_LM2904B
V1: voltage; 12V
V2: voltage; -12V
V3: voltage; PULSE(0 1 0 10n 10n 5m 10m 100); AC 1
V4: voltage; 1
V9: voltage; 1
Named nets: 0, Vcc, Vee, in, CV2, a, out, out1
.ac dec 1000 10 100k
;.tran 0 40m 0 10u
;.step lin param V -2 1 0.1
;.step dec param R 10 10k 100
.MODEL PN4391 NJF(Beta=3.084m Betatce=-500m Rd=1 Rs=1 Lambda=17.5m Vto=-5.27 Vtotc=-2.5m Is=205.2f Isr=1.988p N=1 Nr=2 Xti=3 Alpha=20.98u Vk=123.7 Cgd=5.35p M=406.9m Pb=1 Fc=500m Cgs=4.76p Kf=4.023e-002f Af=1)
.step param R 0.1 100k 1k
;ac dec 1000 10 100k
;.tran 0 40m 0 10u
;.step lin param V -2 1 0.1
;.step param V -2.5 0 0.2
;.step dec param R 10 10k 100
.MODEL PN4391 NJF(Beta=3.084m Betatce=-500m Rd=1 Rs=1 Lambda=17.5m Vto=-5.27 Vtotc=-2.5m Is=205.2f Isr=1.988p N=1 Nr=2 Xti=3 Alpha=20.98u Vk=123.7 Cgd=5.35p M=406.9m Pb=1 Fc=500m Cgs=4.76p Kf=4.023e-002f Af=1)
;.step param R 0.1 100k 1k
