tsedlmeier/Synthesizer/LTSpice/VCF/Draft2.asc

C1: cap; 4.7n
C2: cap; 4.7n
C3: cap; 0.1µ
C5: cap; 2n
C7: cap; 2n
J1: njf; J113
R1: res; 9Meg
R2: res; 3Meg
R3: res; 1Meg
R4: res; 1Meg
R5: res; 100
R6: res; 100k
R7: res; 100k
R8: res; 1k
R9: res; 10k
R10: res; 100k
R11: res; 1k
R12: res; 150k
R13: res; {R}
R14: res; {R}
R15: res; {R}
R16: res; 50k
R17: res; 100
R18: res; 9.9k
U1: LMX58B_LM2904B
U2: LMX58B_LM2904B
U3: LMX58B_LM2904B
V1: voltage; 12V
V2: voltage; -12V
V3: voltage; PULSE(0 1 0 10n 10n 5m 10m 100); AC 1
Named nets: 0, Vcc, Vee, in, a, out
.ac dec 1000 10 100k
;.tran 0 40m 0 10u
.step param R 10k 100k 10k
.MODEL J113 NJF(VTO=-1.2854 BETA=9.25964m BETATCE=-0.5 LAMBDA=3.03839E-2 RD=1.30170 RS=1.30170 CGS=1.05000E-11 CGD=1.20000E-11 PB=5.04493E-1 IS=9.86870E-16 XTI=3 AF=1 FC=0.5 N=1 NR=2 MFG=PHILIPS)
