tsedlmeier/Synthesizer/LTSpice/VCF/VCF_LP2.asc

C1: cap; 0.1µ
C2: cap; 4.7n
C3: cap; 4.7n
C4: cap; 0.1µ
J2: njf; J113
R1: res; 100k
R2: res; 10Meg
R3: res; 3Meg
R4: res; 1Meg
R5: res; 1Meg
R6: res; 100k
R7: res; 100k
R8: res; 1k
R9: res; 10k
R10: res; 100k
R11: res; 1k
R12: res; 150k
R13: res; 100k
R14: res; 100k
R15: res; 50k
R16: res; 50k
R17: res; 100
R18: res; 9.9k
U1: LMX58B_LM2904B
U2: LMX58B_LM2904B
V1: voltage; 12V
V2: voltage; -12V
V3: voltage; PULSE(0 1 0 10n 10n 5m 10m 100); AC 1
V5: voltage; {V}
Named nets: 0, Vcc, Vee, in, out, CV1, CV2, a
.ac dec 1000 10 100k
;.tran 0 40m 0 10u
.step param V -2.5 2.5 0.2
.MODEL PN4391 NJF(Beta=3.084m Betatce=-500m Rd=1 Rs=1 Lambda=17.5m Vto=-5.27 Vtotc=-2.5m Is=205.2f Isr=1.988p N=1 Nr=2 Xti=3 Alpha=20.98u Vk=123.7 Cgd=5.35p M=406.9m Pb=1 Fc=500m Cgs=4.76p Kf=4.023e-002f Af=1)
;.step param R 0.1 100k 5k
.MODEL J113 NJF(VTO=-1.2854 BETA=9.25964m BETATCE=-0.5 LAMBDA=3.03839E-2 RD=1.30170 RS=1.30170 CGS=1.05000E-11 CGD=1.20000E-11 PB=5.04493E-1 IS=9.86870E-16 XTI=3 AF=1 FC=0.5 N=1 NR=2 MFG=PHILIPS)
