tsedlmeier/Synthesizer/LTSpice/VCF/VCF_HP1.asc

C3: cap; 0.1µ
C4: cap; 1µ
C5: cap; 2.2n
J1: njf
R1: res; 3Meg
R2: res; 3Meg
R3: res; 1.5Meg
R4: res; 1.5Meg
R5: res; 100
U1: LMX58B_LM2904B
V1: voltage; 12V
V2: voltage; -12V
V3: voltage; PULSE(0 1 0 10n 10n 0.5m 1m 100); AC 1
V4: voltage; {V}
Named nets: 0, Vcc, Vee, in, out, a
.step lin param V -2 1 0.1
.ac dec 1000 10 100k
;tran 0 40m 0 10u
